kev-ju/PC-Retro-MTM/64_256KB_SYSTEM_BOARD.kicad_sch

## KiCad design 64_256KB_SYSTEM_BOARD.kicad_sch (2026-03-31)

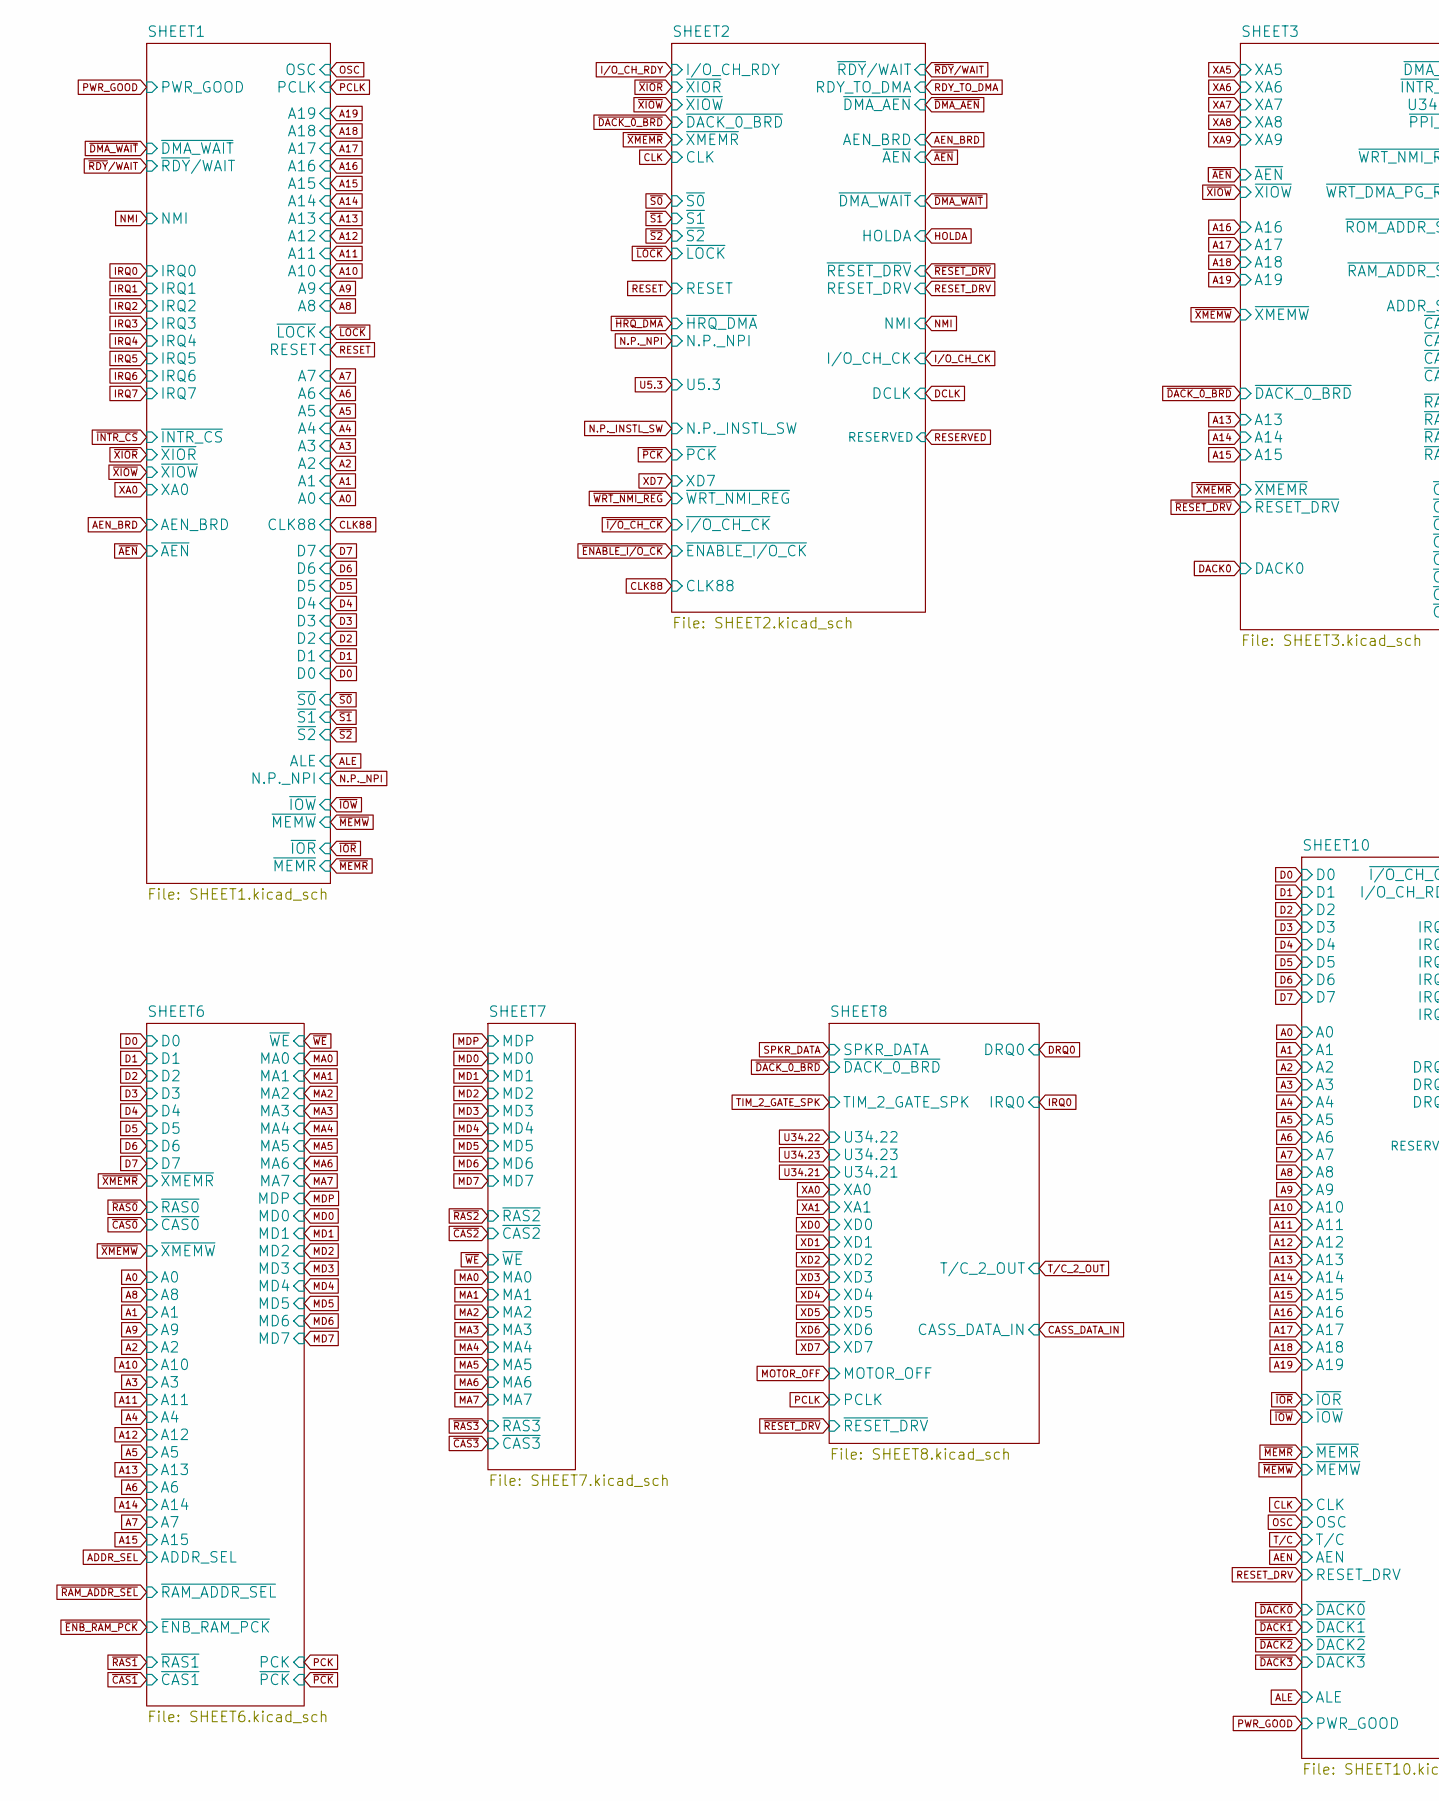
[picture p4: schematic 64_256KB_SYSTEM_BOARD.kicad_sch, part in row 1, column 1]

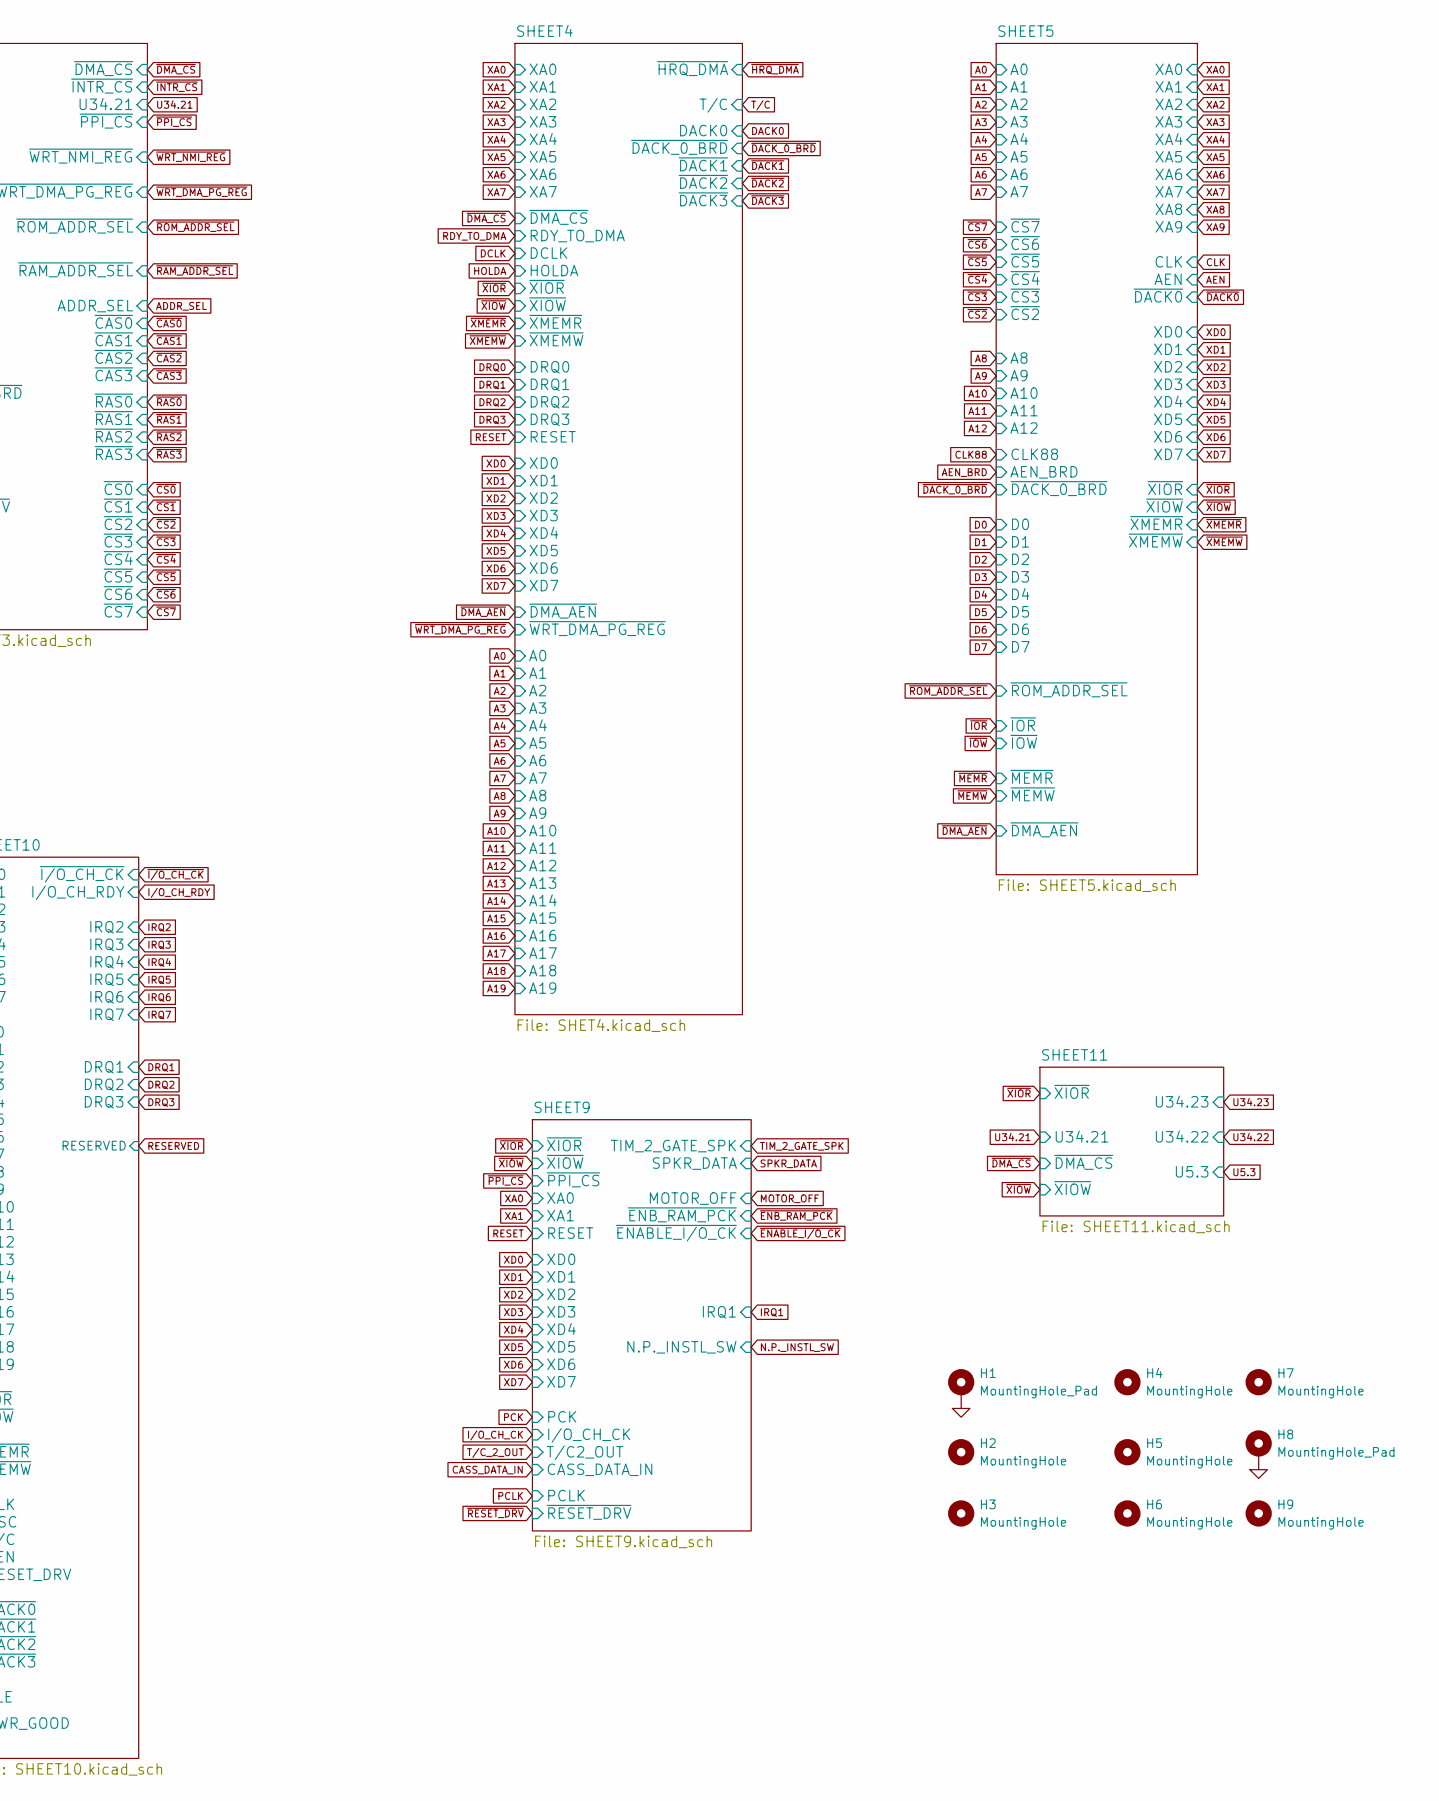
[picture p5: schematic 64_256KB_SYSTEM_BOARD.kicad_sch, part in row 1, column 2]

Parts:
H1, H8: MountingHole_Pad; PLATED_HOLE
H2, H3, H4, H5, H6, H7, H9: MountingHole; HOLE

Connections:
GND: H1.1, H8.1
