kev-ju/PC-Retro-MTM/SHEET1.kicad_sch

## KiCad design SHEET1.kicad_sch (2026-03-31)

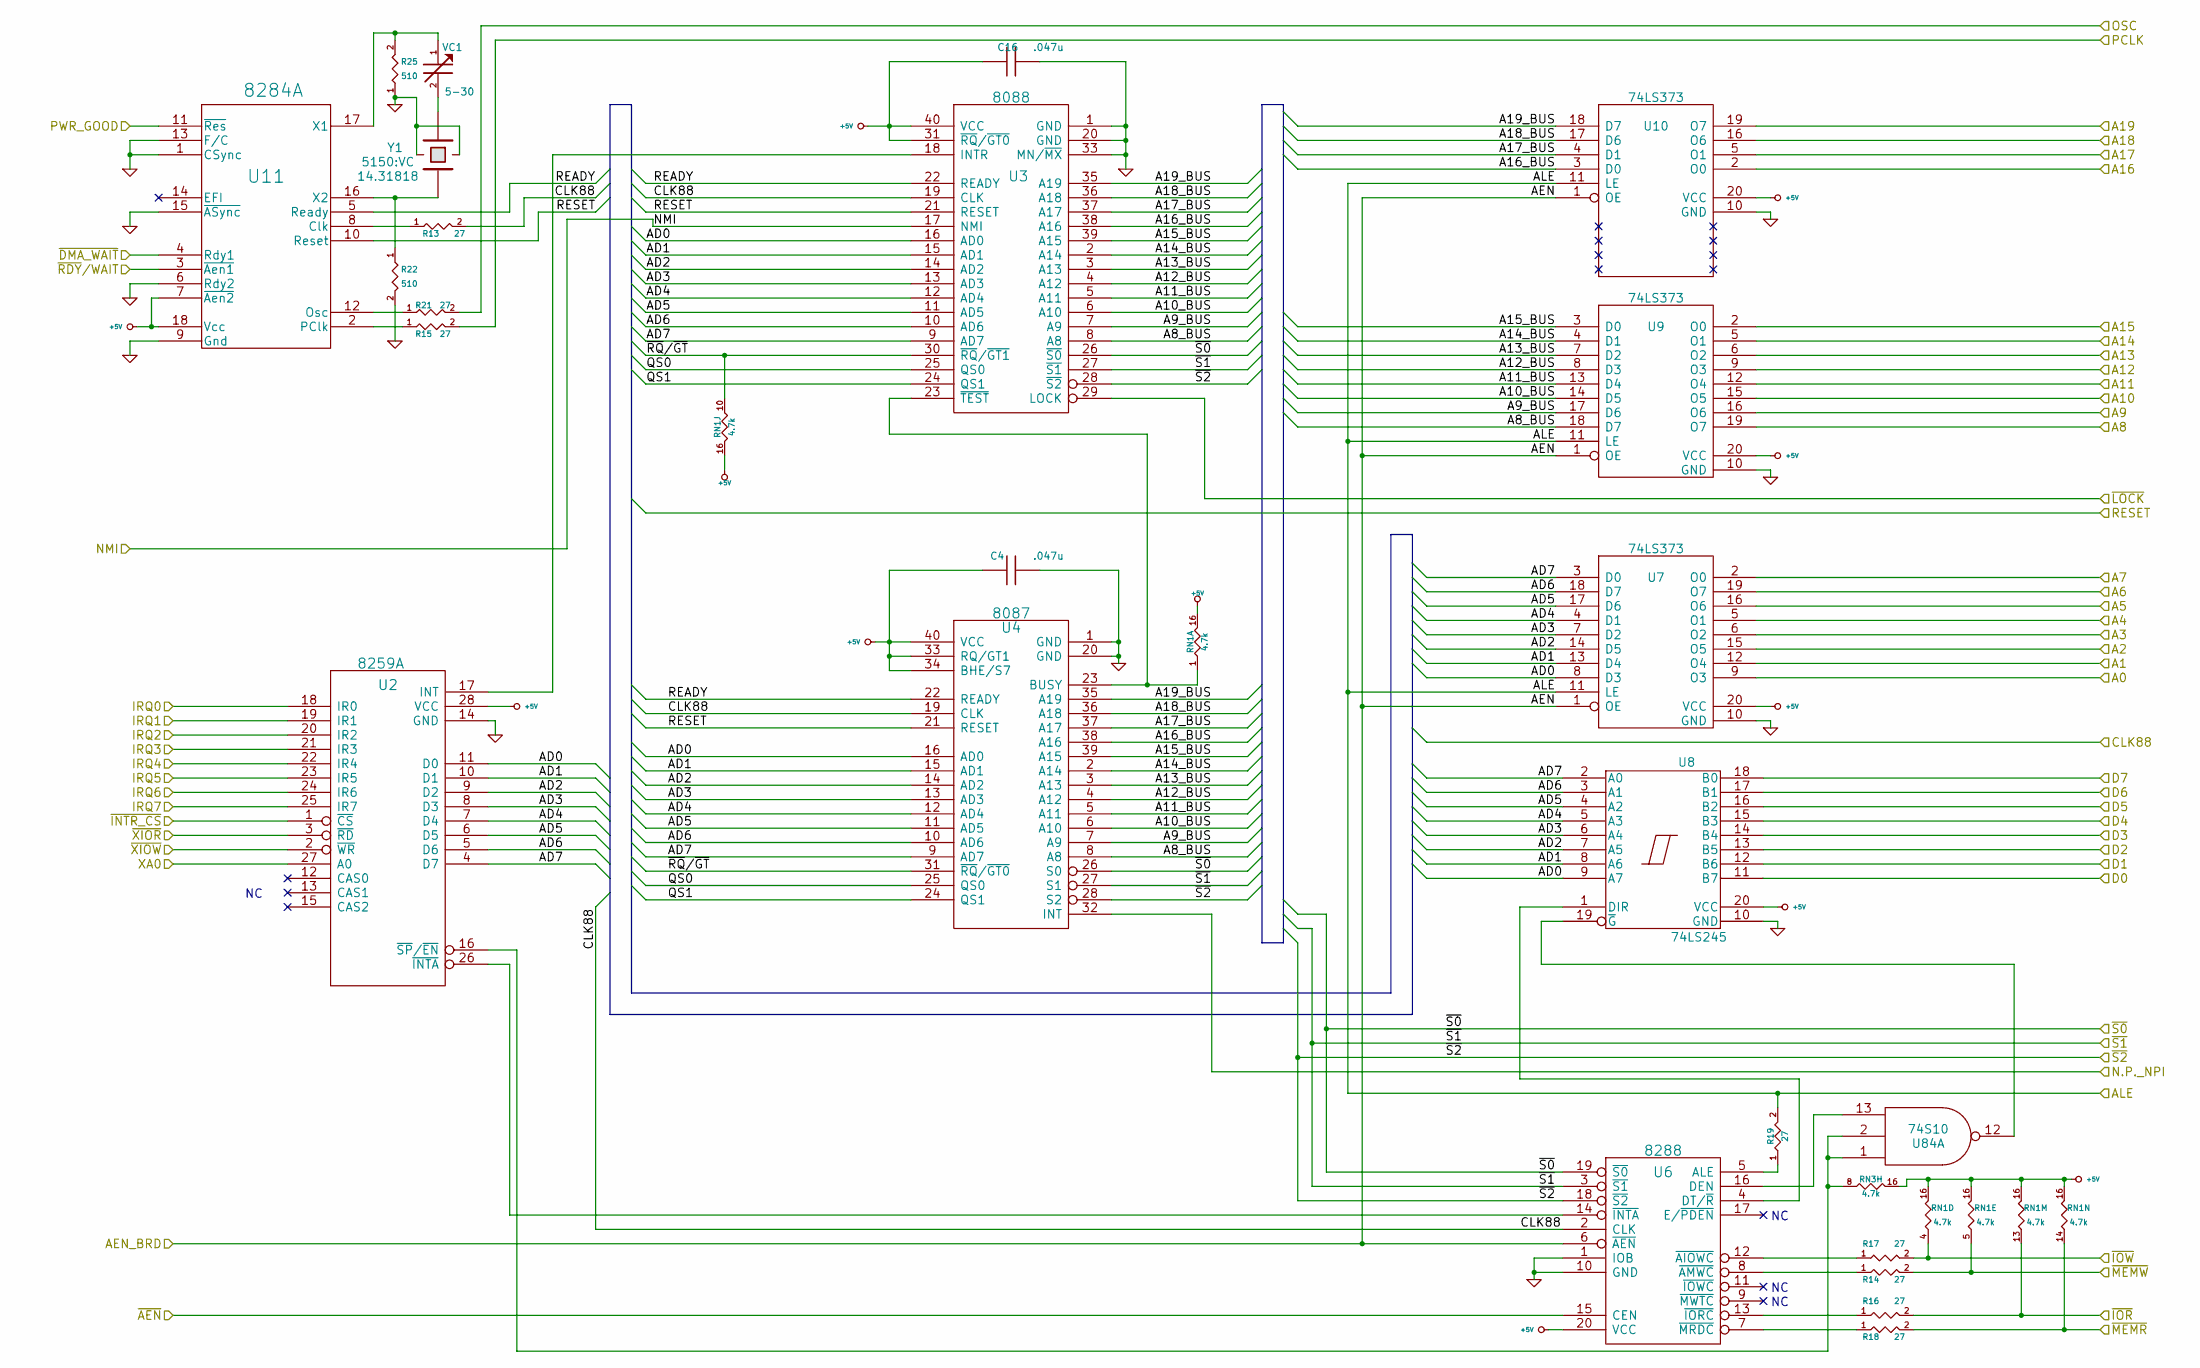
[picture p6: schematic SHEET1.kicad_sch]

Parts:
C4, C16: .047u; C_254_508_2PIN
R13, R14, R15, R16, R17, R18, R19, R21: 27; R5
R22, R25: 510; R5
RN1, RN3: 4.7k; DIP-16__300
U2: 8259A; DIP-28__600
U3: 8088; DIP-40__600
U4: 8087; DIP-40__600
U6: 8288; DIP-20__300
U7, U9, U10: 74LS373; DIP-20__300
U8: 74LS245; DIP-20__300
U11: 8284A; DIP-18__300
U84: 74S10; DIP-14__300
VC1: 5-30; VR
Y1: 14.31818; VC

Connections:
+5V: C4.2, C16.2, RN1.16, RN3.16, U2.28 (VCC), U3.31 (~RQ/~GT0), U3.40 (VCC), U4.33 (RQ/GT1), U4.34 (BHE/S7), U4.40 (VCC), U6.20 (VCC), U7.20 (VCC), U8.20 (VCC), U9.20 (VCC), U10.20 (VCC), U11.7 (~Aen2), U11.18 (Vcc)
A0: U7.9 (O3)
A1: U7.12 (O4)
A2: U7.15 (O5)
A3: U7.6 (O2)
A4: U7.5 (O1)
A5: U7.16 (O6)
A6: U7.19 (O7)
A7: U7.2 (O0)
A8: U9.19 (O7)
A8_BUS: U3.8 (A8), U4.8 (A8), U9.18 (D7)
A9: U9.16 (O6)
A9_BUS: U3.7 (A9), U4.7 (A9), U9.17 (D6)
A10: U9.15 (O5)
A10_BUS: U3.6 (A10), U4.6 (A10), U9.14 (D5)
A11: U9.12 (O4)
A11_BUS: U3.5 (A11), U4.5 (A11), U9.13 (D4)
A12: U9.9 (O3)
A12_BUS: U3.4 (A12), U4.4 (A12), U9.8 (D3)
A13: U9.6 (O2)
A13_BUS: U3.3 (A13), U4.3 (A13), U9.7 (D2)
A14: U9.5 (O1)
A14_BUS: U3.2 (A14), U4.2 (A14), U9.4 (D1)
A15: U9.2 (O0)
A15_BUS: U3.39 (A15), U4.39 (A15), U9.3 (D0)
A16: U10.2 (O0)
A16_BUS: U3.38 (A16), U4.38 (A16), U10.3 (D0)
A17: U10.5 (O1)
A17_BUS: U3.37 (A17), U4.37 (A17), U10.4 (D1)
A18: U10.16 (O6)
A18_BUS: U3.36 (A18), U4.36 (A18), U10.17 (D6)
A19: U10.19 (O7)
A19_BUS: U3.35 (A19), U4.35 (A19), U10.18 (D7)
AD0: U2.11 (D0), U3.16 (AD0), U4.16 (AD0), U7.8 (D3), U8.9 (A7)
AD1: U2.10 (D1), U3.15 (AD1), U4.15 (AD1), U7.13 (D4), U8.8 (A6)
AD2: U2.9 (D2), U3.14 (AD2), U4.14 (AD2), U7.14 (D5), U8.7 (A5)
AD3: U2.8 (D3), U3.13 (AD3), U4.13 (AD3), U7.7 (D2), U8.6 (A4)
AD4: U2.7 (D4), U3.12 (AD4), U4.12 (AD4), U7.4 (D1), U8.5 (A3)
AD5: U2.6 (D5), U3.11 (AD5), U4.11 (AD5), U7.17 (D6), U8.4 (A2)
AD6: U2.5 (D6), U3.10 (AD6), U4.10 (AD6), U7.18 (D7), U8.3 (A1)
AD7: U2.4 (D7), U3.9 (AD7), U4.9 (AD7), U7.3 (D0), U8.2 (A0)
AEN: U6.6 (~AEN), U7.1 (OE), U9.1 (OE), U10.1 (OE)
ALE: R19.2, U7.11 (LE), U9.11 (LE), U10.11 (LE)
CLK88: R13.2, U3.19 (CLK), U4.19 (CLK), U6.2 (CLK)
D0: U8.11 (B7)
D1: U8.12 (B6)
D2: U8.13 (B5)
D3: U8.14 (B4)
D4: U8.15 (B3)
D5: U8.16 (B2)
D6: U8.17 (B1)
D7: U8.18 (B0)
GND: C4.1, C16.1, R22.2, R25.1, U2.14 (GND), U3.1 (GND), U3.20 (GND), U3.33 (MN/~MX), U4.1 (GND), U4.20 (GND), U6.1 (IOB), U6.10 (GND), U7.10 (GND), U8.10 (GND), U9.10 (GND), U10.10 (GND), U11.1 (CSync), U11.6 (Rdy2), U11.9 (Gnd), U11.13 (F/C), U11.15 (~ASync), Y1.3 (GND), Y1.4 (GND)
IRQ0: U2.18 (IR0)
IRQ1: U2.19 (IR1)
IRQ2: U2.20 (IR2)
IRQ3: U2.21 (IR3)
IRQ4: U2.22 (IR4)
IRQ5: U2.23 (IR5)
IRQ6: U2.24 (IR6)
IRQ7: U2.25 (IR7)
N.P._NPI: U4.32 (INT)
NMI: U3.17 (NMI)
unnamed: R13.1, U11.8 (Clk)
unnamed: R14.1, U6.8 (~AMWC)
unnamed: R15.1, U11.2 (PClk)
unnamed: R16.1, U6.13 (~IORC)
unnamed: R17.1, U6.12 (~AIOWC)
unnamed: R18.1, U6.7 (~MRDC)
unnamed: R19.1, U6.5 (ALE)
unnamed: R21.1, U11.12 (Osc)
unnamed: R22.1, U11.16 (X2), Y1.2
unnamed: R25.2, U11.17 (X1), VC1.1
unnamed: RN1.1 (P15), U3.23 (~TEST), U4.23 (BUSY)
unnamed: RN3.8 (P15), U2.16 (~SP/~EN), U84.1, U84.2
unnamed: U2.17 (INT), U3.18 (INTR)
unnamed: U2.26 (~INTA), U6.14 (~INTA)
unnamed: U6.4 (DT/~R), U8.1 (DIR)
unnamed: U6.16 (DEN), U84.13
unnamed: U8.19 (~G), U84.12
unnamed: VC1.2, Y1.1
OSC: R21.2
PCLK: R15.2
PWR_GOOD: U11.11 (~Res)
QS0: U3.25 (QS0), U4.25 (QS0)
QS1: U3.24 (QS1), U4.24 (QS1)
READY: U3.22 (READY), U4.22 (READY), U11.5 (Ready)
RESET: U3.21 (RESET), U4.21 (RESET), U11.10 (Reset)
XA0: U2.27 (A0)
~AEN: U6.15 (CEN)
~DMA_WAIT: U11.4 (Rdy1)
~INTR_CS: U2.1 (~CS)
~IOR: R16.2, RN1.13 (P15)
~IOW: R17.2, RN1.4 (P15)
~LOCK: U3.29 (LOCK)
~MEMR: R18.2, RN1.14 (P15)
~MEMW: R14.2, RN1.5 (P15)
~RDY/WAIT: U11.3 (~Aen1)
~RQ/~GT: RN1.10 (P15), U3.30 (~RQ/~GT1), U4.31 (~RQ/~GT0)
~S0: U3.26 (~S0), U4.26 (S0), U6.19 (~S0)
~S1: U3.27 (~S1), U4.27 (S1), U6.3 (~S1)
~S2: U3.28 (~S2), U4.28 (S2), U6.18 (~S2)
~XIOR: U2.3 (~RD)
~XIOW: U2.2 (~WR)
