kev-ju/PC-Retro-MTM/SHEET2.kicad_sch

## KiCad design SHEET2.kicad_sch (2026-03-31)

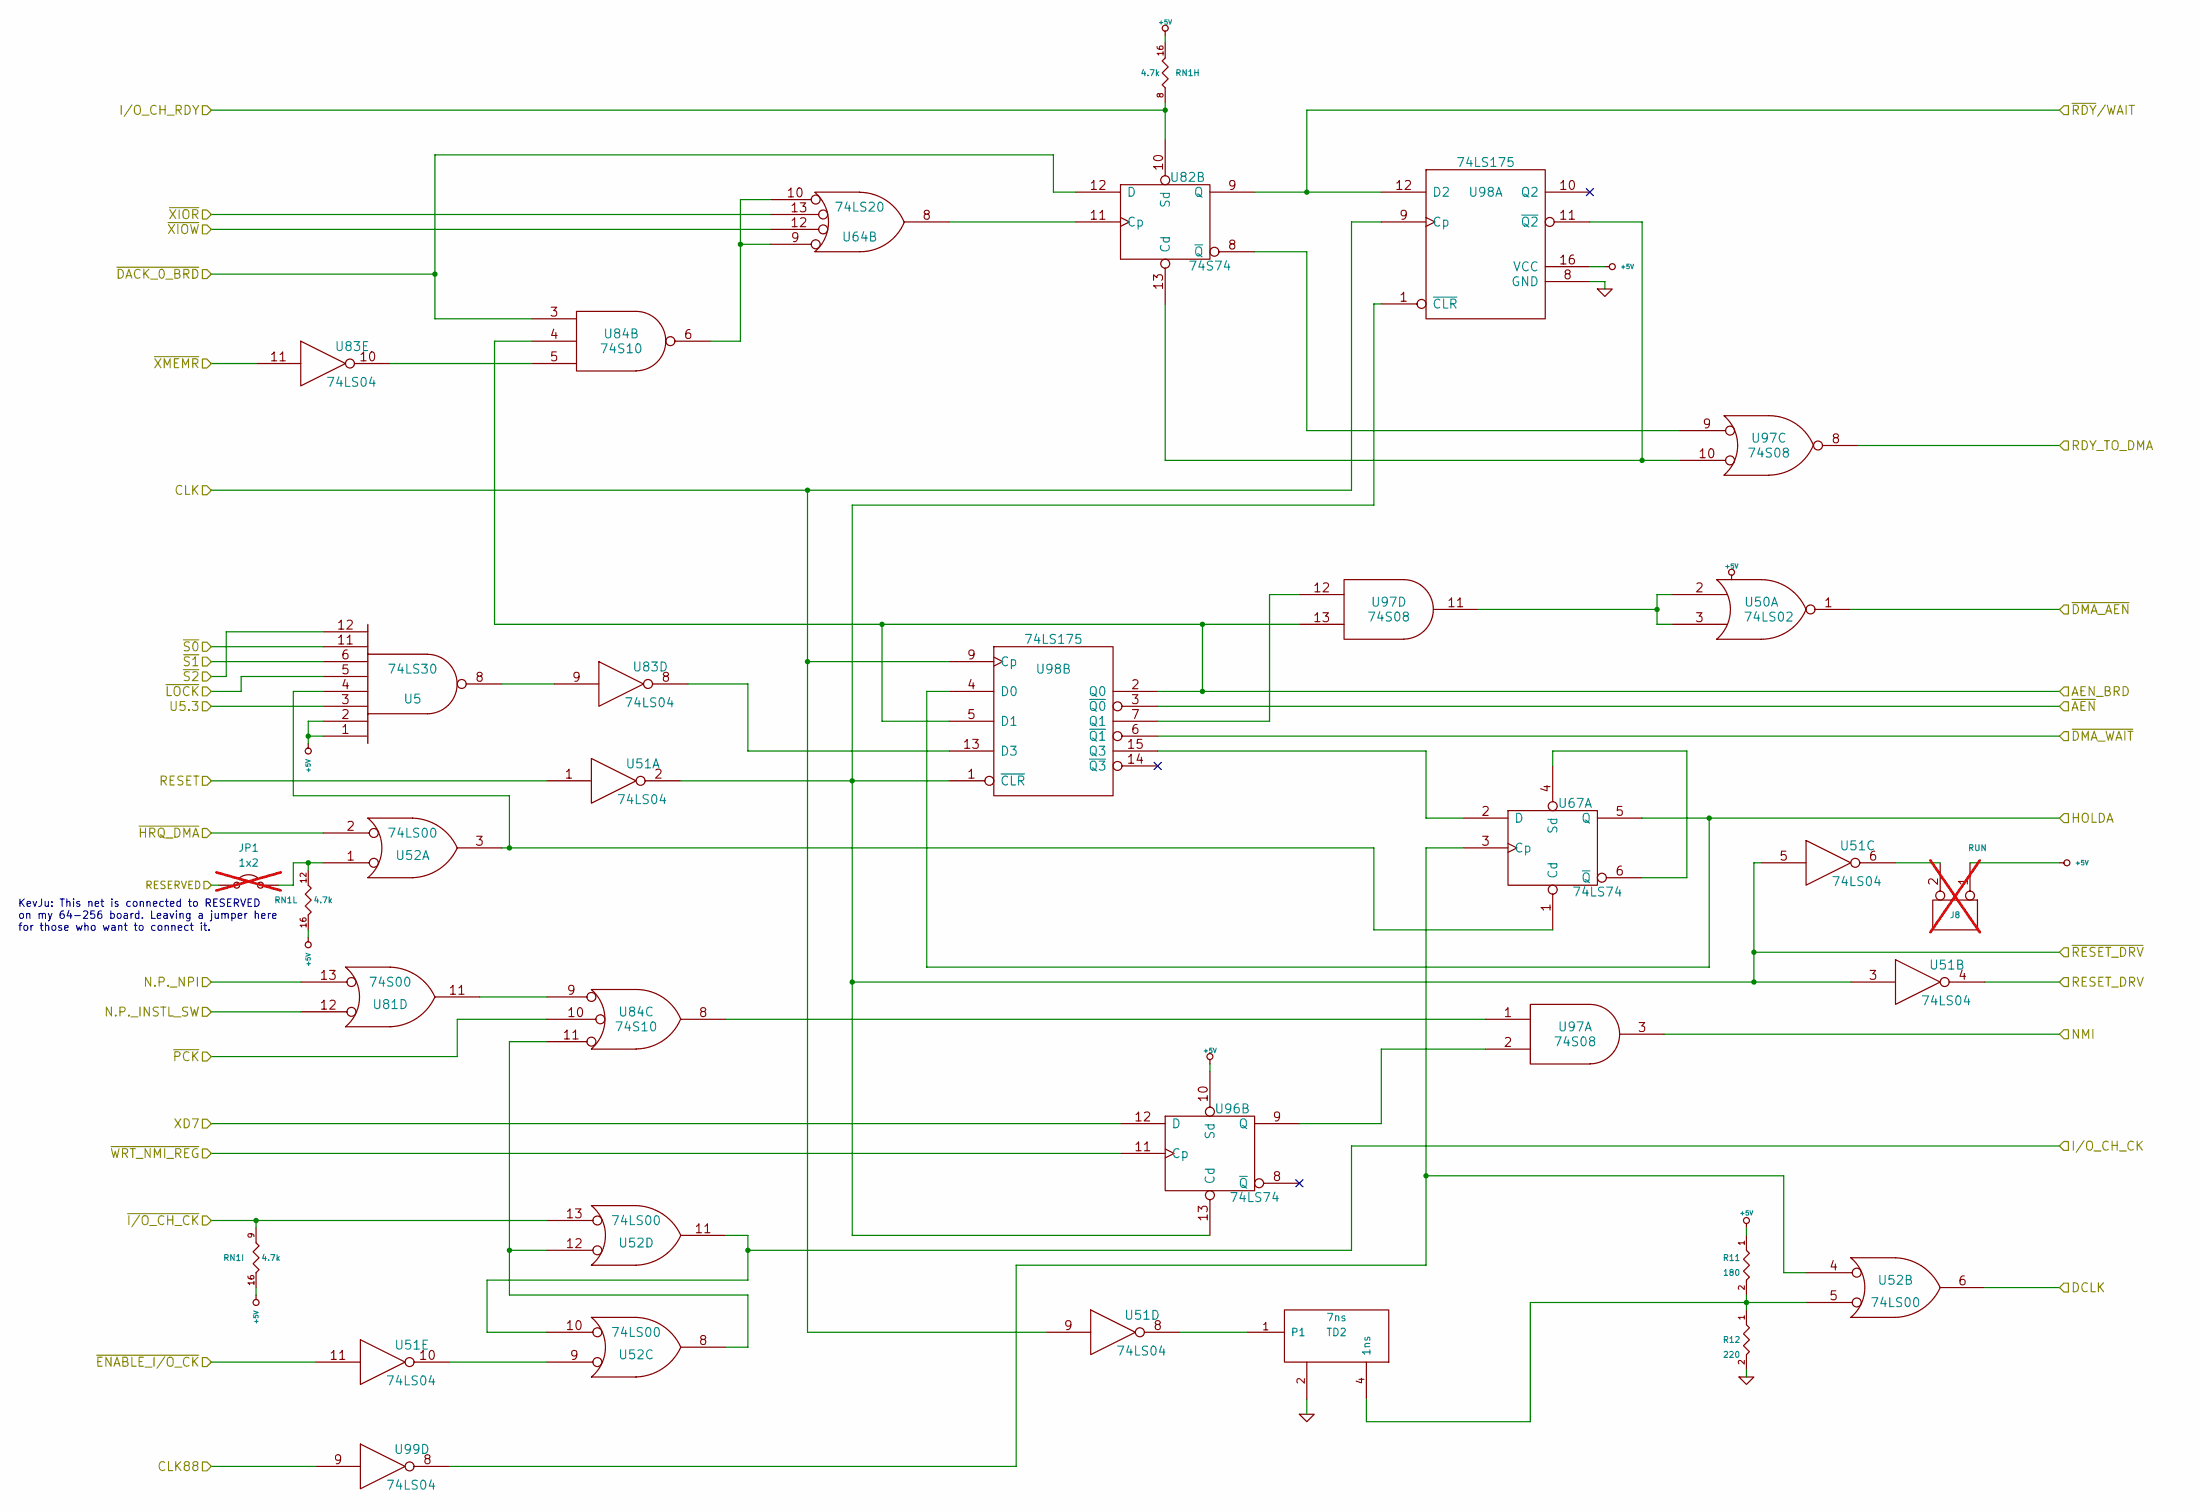
[picture p7: schematic SHEET2.kicad_sch]

Parts:
J8: RUN; PIN_ARRAY_2X1; not fitted
JP1: 1x2; PinHeader_1x02_P2.54mm_Vertical; not fitted
R11: 180; R5
R12: 220; R5
RN1: 4.7k; DIP-16__300
TD2: 7ns; TD2
U5: 74LS30; DIP-14__300
U50: 74LS02; DIP-14__300
U51, U83, U99: 74LS04; DIP-14__300
U52: 74LS00; DIP-14__300
U64: 74LS20; DIP-14__300
U67, U96: 74LS74; DIP-14__300
U81: 74S00; DIP-14__300
U82: 74S74; DIP-14__300
U84: 74S10; DIP-14__300
U97: 74S08; DIP-14__300
U98: 74LS175; DIP-16__300

Connections:
+5V: J8.1, R11.1, RN1.16, U5.1, U5.2, U50.14 (VCC), U96.10 (Sd), U98.16 (VCC)
AEN_BRD: U84.4, U97.13, U98.2 (Q0), U98.5 (D1)
CLK: U51.9, U98.9 (Cp)
CLK88: U99.9
DCLK: U52.6
GND: R12.2, TD2.2, U98.8 (GND)
HOLDA: U67.5 (Q), U98.4 (D0)
I/O_CH_CK: U52.10, U52.11
I/O_CH_RDY: RN1.8 (P15), U82.10 (Sd)
N.P._INSTL_SW: U81.12
N.P._NPI: U81.13
NMI: U97.3
unnamed: J8.2 (PM), U51.6
unnamed: JP1.2 (B), RN1.12 (P15), U52.1
unnamed: R11.2, R12.1, TD2.4 (1ns), U52.5
unnamed: TD2.1, U51.8
unnamed: U5.4, U52.3, U67.1 (Cd)
unnamed: U5.8, U83.9
unnamed: U50.2, U50.3, U97.11
unnamed: U51.10, U52.9
unnamed: U52.4, U67.3 (Cp), U99.8
unnamed: U52.8, U52.12, U84.11
unnamed: U64.8, U82.11 (Cp)
unnamed: U64.9, U64.13, U84.6
unnamed: U67.2 (D), U98.15 (Q3)
unnamed: U67.4 (Sd), U67.6 (~Q)
unnamed: U81.11, U84.9
unnamed: U82.8 (~Q), U97.9
unnamed: U82.13 (Cd), U97.10, U98.11 (~Q2)
unnamed: U83.8, U98.13 (D3)
unnamed: U83.10, U84.5
unnamed: U84.8, U97.1
unnamed: U96.9 (Q), U97.2
unnamed: U97.12, U98.7 (Q1)
RDY_TO_DMA: U97.8
RESERVED: JP1.1 (A)
RESET: U51.1
RESET_DRV: U51.4
U5.3: U5.3
XD7: U96.12 (D)
~AEN: U98.3 (~Q0)
~DACK_0_BRD: U82.12 (D), U84.3
~DMA_AEN: U50.1
~DMA_WAIT: U98.6 (~Q1)
~ENABLE_I/O_CK: U51.11
~HRQ_DMA: U52.2
~I/O_CH_CK: RN1.9 (P15), U52.13
~LOCK: U5.5
~PCK: U84.10
~RDY/WAIT: U82.9 (Q), U98.12 (D2)
~RESET_DRV: U51.2, U51.3, U51.5, U96.13 (Cd), U98.1 (~CLR)
~S0: U5.11
~S1: U5.6
~S2: U5.12
~WRT_NMI_REG: U96.11 (Cp)
~XIOR: U64.12
~XIOW: U64.10
~XMEMR: U83.11

Notes on the sheet:
KevJu: This net is connected to RESERVED on my 64-256 board. Leaving a jumper here for those who want to connect it.
