kev-ju/PC-Retro-MTM/SHEET3.kicad_sch

## KiCad design SHEET3.kicad_sch (2026-03-31)

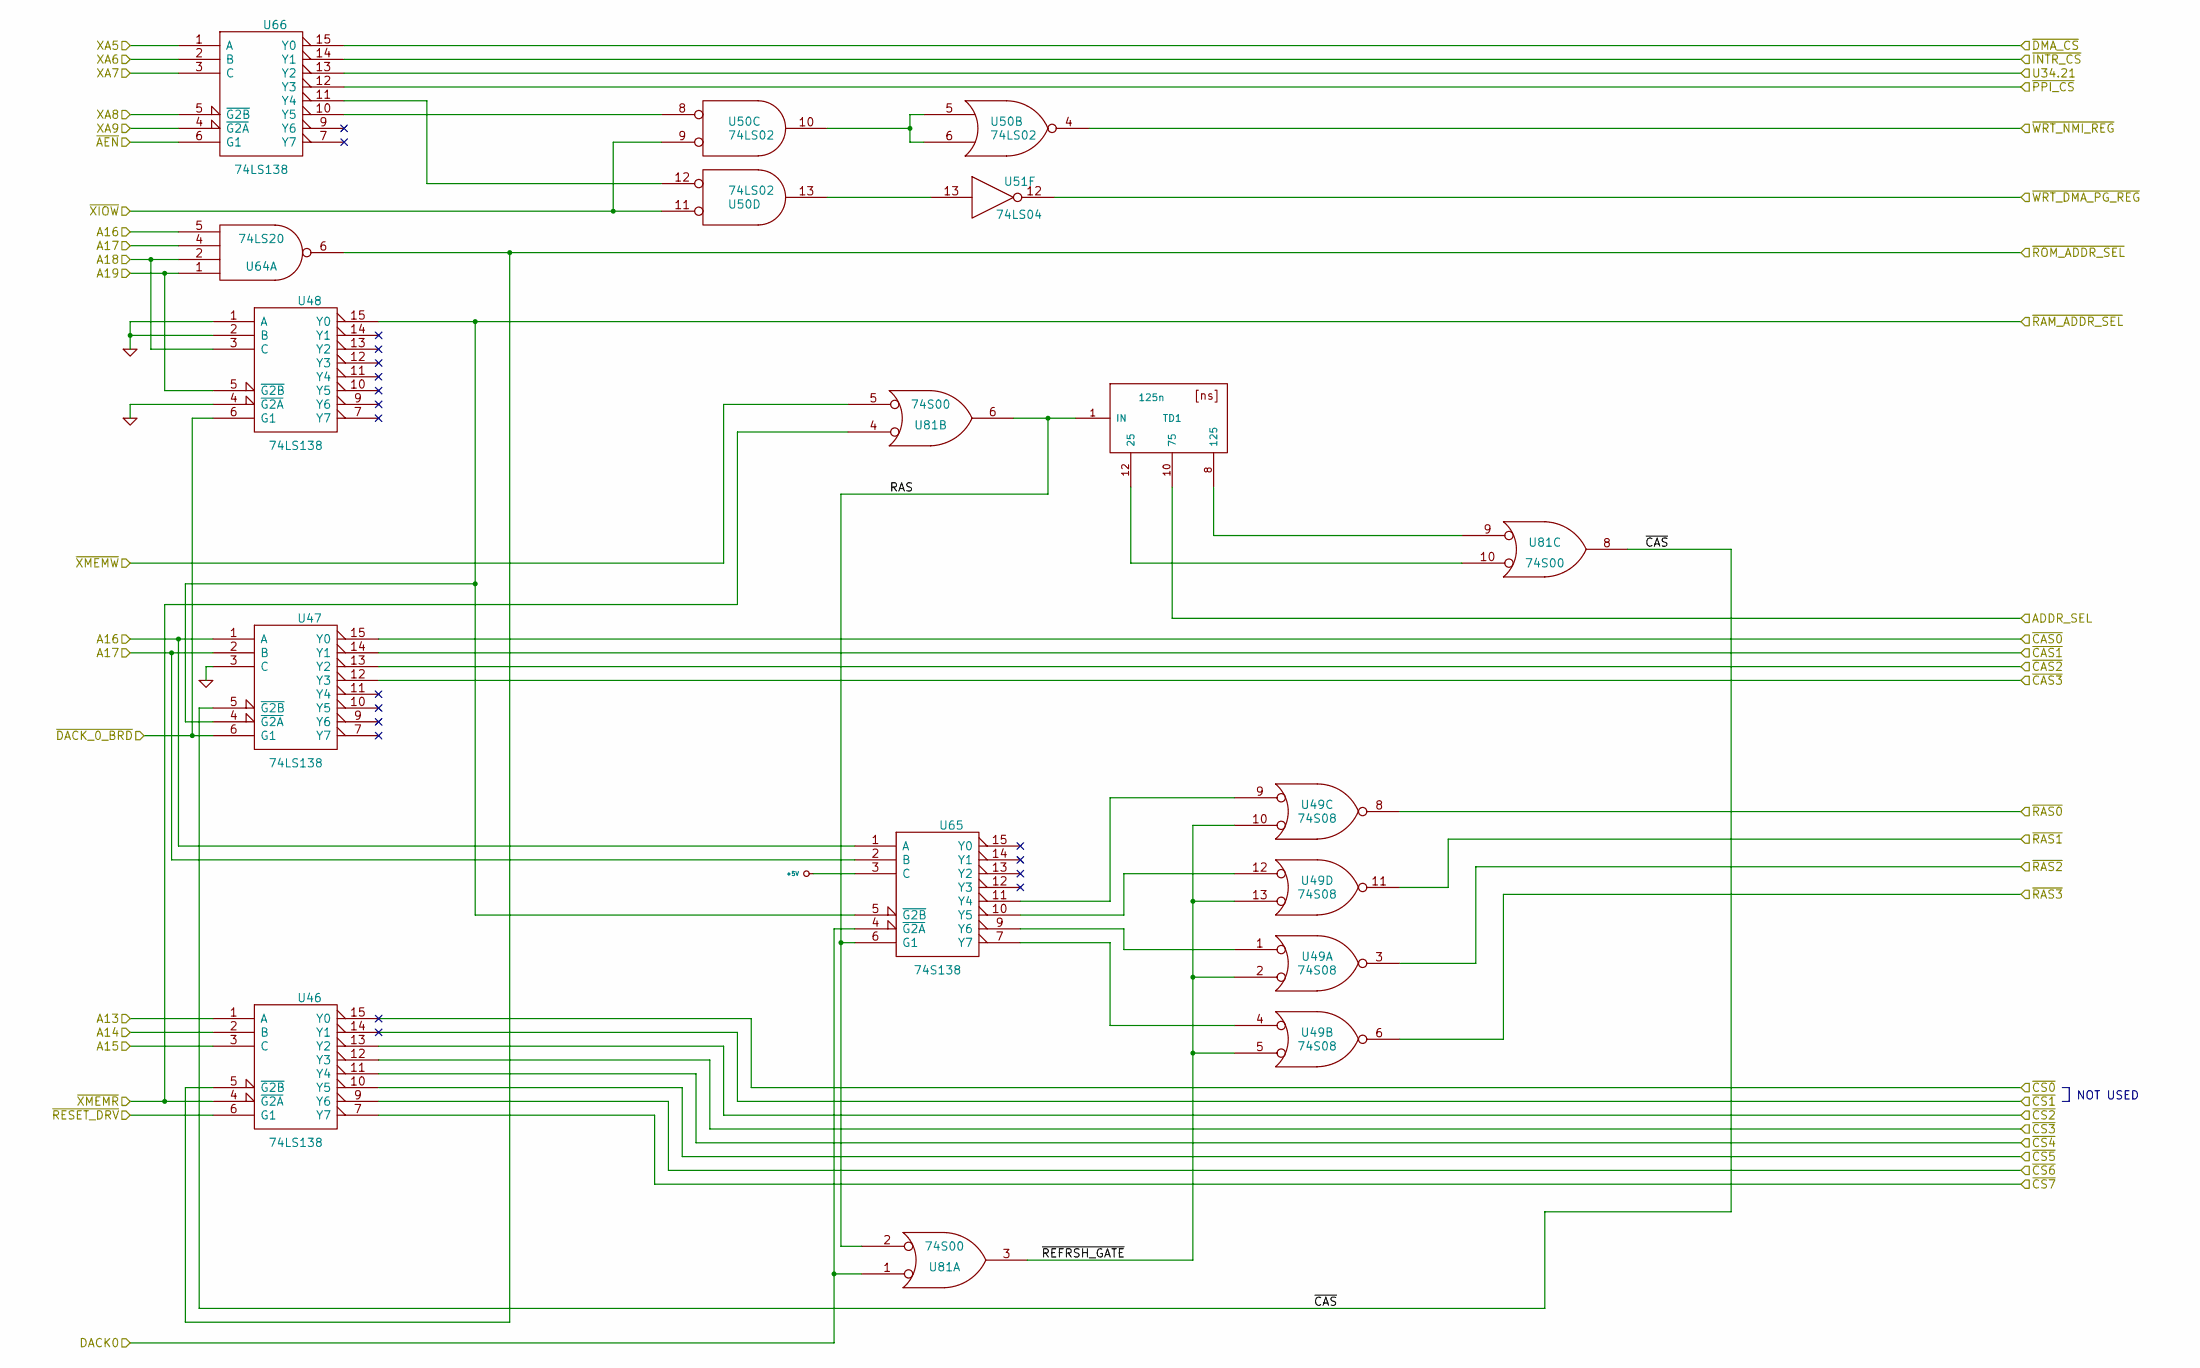
[picture p8: schematic SHEET3.kicad_sch]

Parts:
TD1: 125n; TD1
U46, U47, U48, U66: 74LS138; DIP-16__300
U49: 74S08; DIP-14__300
U50: 74LS02; DIP-14__300
U51: 74LS04; DIP-14__300
U64: 74LS20; DIP-14__300
U65: 74S138; DIP-16__300
U81: 74S00; DIP-14__300

Connections:
+5V: U65.3 (C)
A13: U46.1 (A)
A14: U46.2 (B)
A15: U46.3 (C)
A16: U47.1 (A), U64.5, U65.1 (A)
A17: U47.2 (B), U64.4, U65.2 (B)
A18: U48.3 (C), U64.2
A19: U48.5 (~G2B), U64.1
ADDR_SEL: TD1.10 (75)
DACK0: U65.4 (~G2A), U81.1
GND: U47.3 (C), U48.1 (A), U48.2 (B), U48.4 (~G2A)
unnamed: TD1.8 (125), U81.9
unnamed: TD1.12 (25), U81.10
unnamed: U49.1, U65.9 (Y6)
unnamed: U49.4, U65.7 (Y7)
unnamed: U49.9, U65.11 (Y4)
unnamed: U49.12, U65.10 (Y5)
unnamed: U50.8, U66.10 (Y5)
unnamed: U50.5, U50.6, U50.10
unnamed: U50.12, U66.11 (Y4)
unnamed: U50.13, U51.13
RAS: TD1.1 (IN), U65.6 (G1), U81.2, U81.6
U34.21: U66.13 (Y2)
XA5: U66.1 (A)
XA6: U66.2 (B)
XA7: U66.3 (C)
XA8: U66.5 (~G2B)
XA9: U66.4 (~G2A)
~AEN: U66.6 (G1)
~CAS0: U47.15 (Y0)
~CAS1: U47.14 (Y1)
~CAS2: U47.13 (Y2)
~CAS3: U47.12 (Y3)
~CAS: U47.5 (~G2B), U81.8
~CS0: U46.15 (Y0)
~CS1: U46.14 (Y1)
~CS2: U46.13 (Y2)
~CS3: U46.12 (Y3)
~CS4: U46.11 (Y4)
~CS5: U46.10 (Y5)
~CS6: U46.9 (Y6)
~CS7: U46.7 (Y7)
~DACK_0_BRD: U47.6 (G1), U48.6 (G1)
~DMA_CS: U66.15 (Y0)
~INTR_CS: U66.14 (Y1)
~PPI_CS: U66.12 (Y3)
~RAM_ADDR_SEL: U47.4 (~G2A), U48.15 (Y0), U65.5 (~G2B)
~RAS0: U49.8
~RAS1: U49.11
~RAS2: U49.3
~RAS3: U49.6
~REFRSH_GATE: U49.2, U49.5, U49.10, U49.13, U81.3
~RESET_DRV: U46.6 (G1)
~ROM_ADDR_SEL: U46.5 (~G2B), U64.6
~WRT_DMA_PG_REG: U51.12
~WRT_NMI_REG: U50.4
~XIOW: U50.9, U50.11
~XMEMR: U46.4 (~G2A), U81.4
~XMEMW: U81.5

Notes on the sheet:
NOT USED
