kev-ju/PC-Retro-MTM/SHEET5.kicad_sch

## KiCad design SHEET5.kicad_sch (2026-03-31)

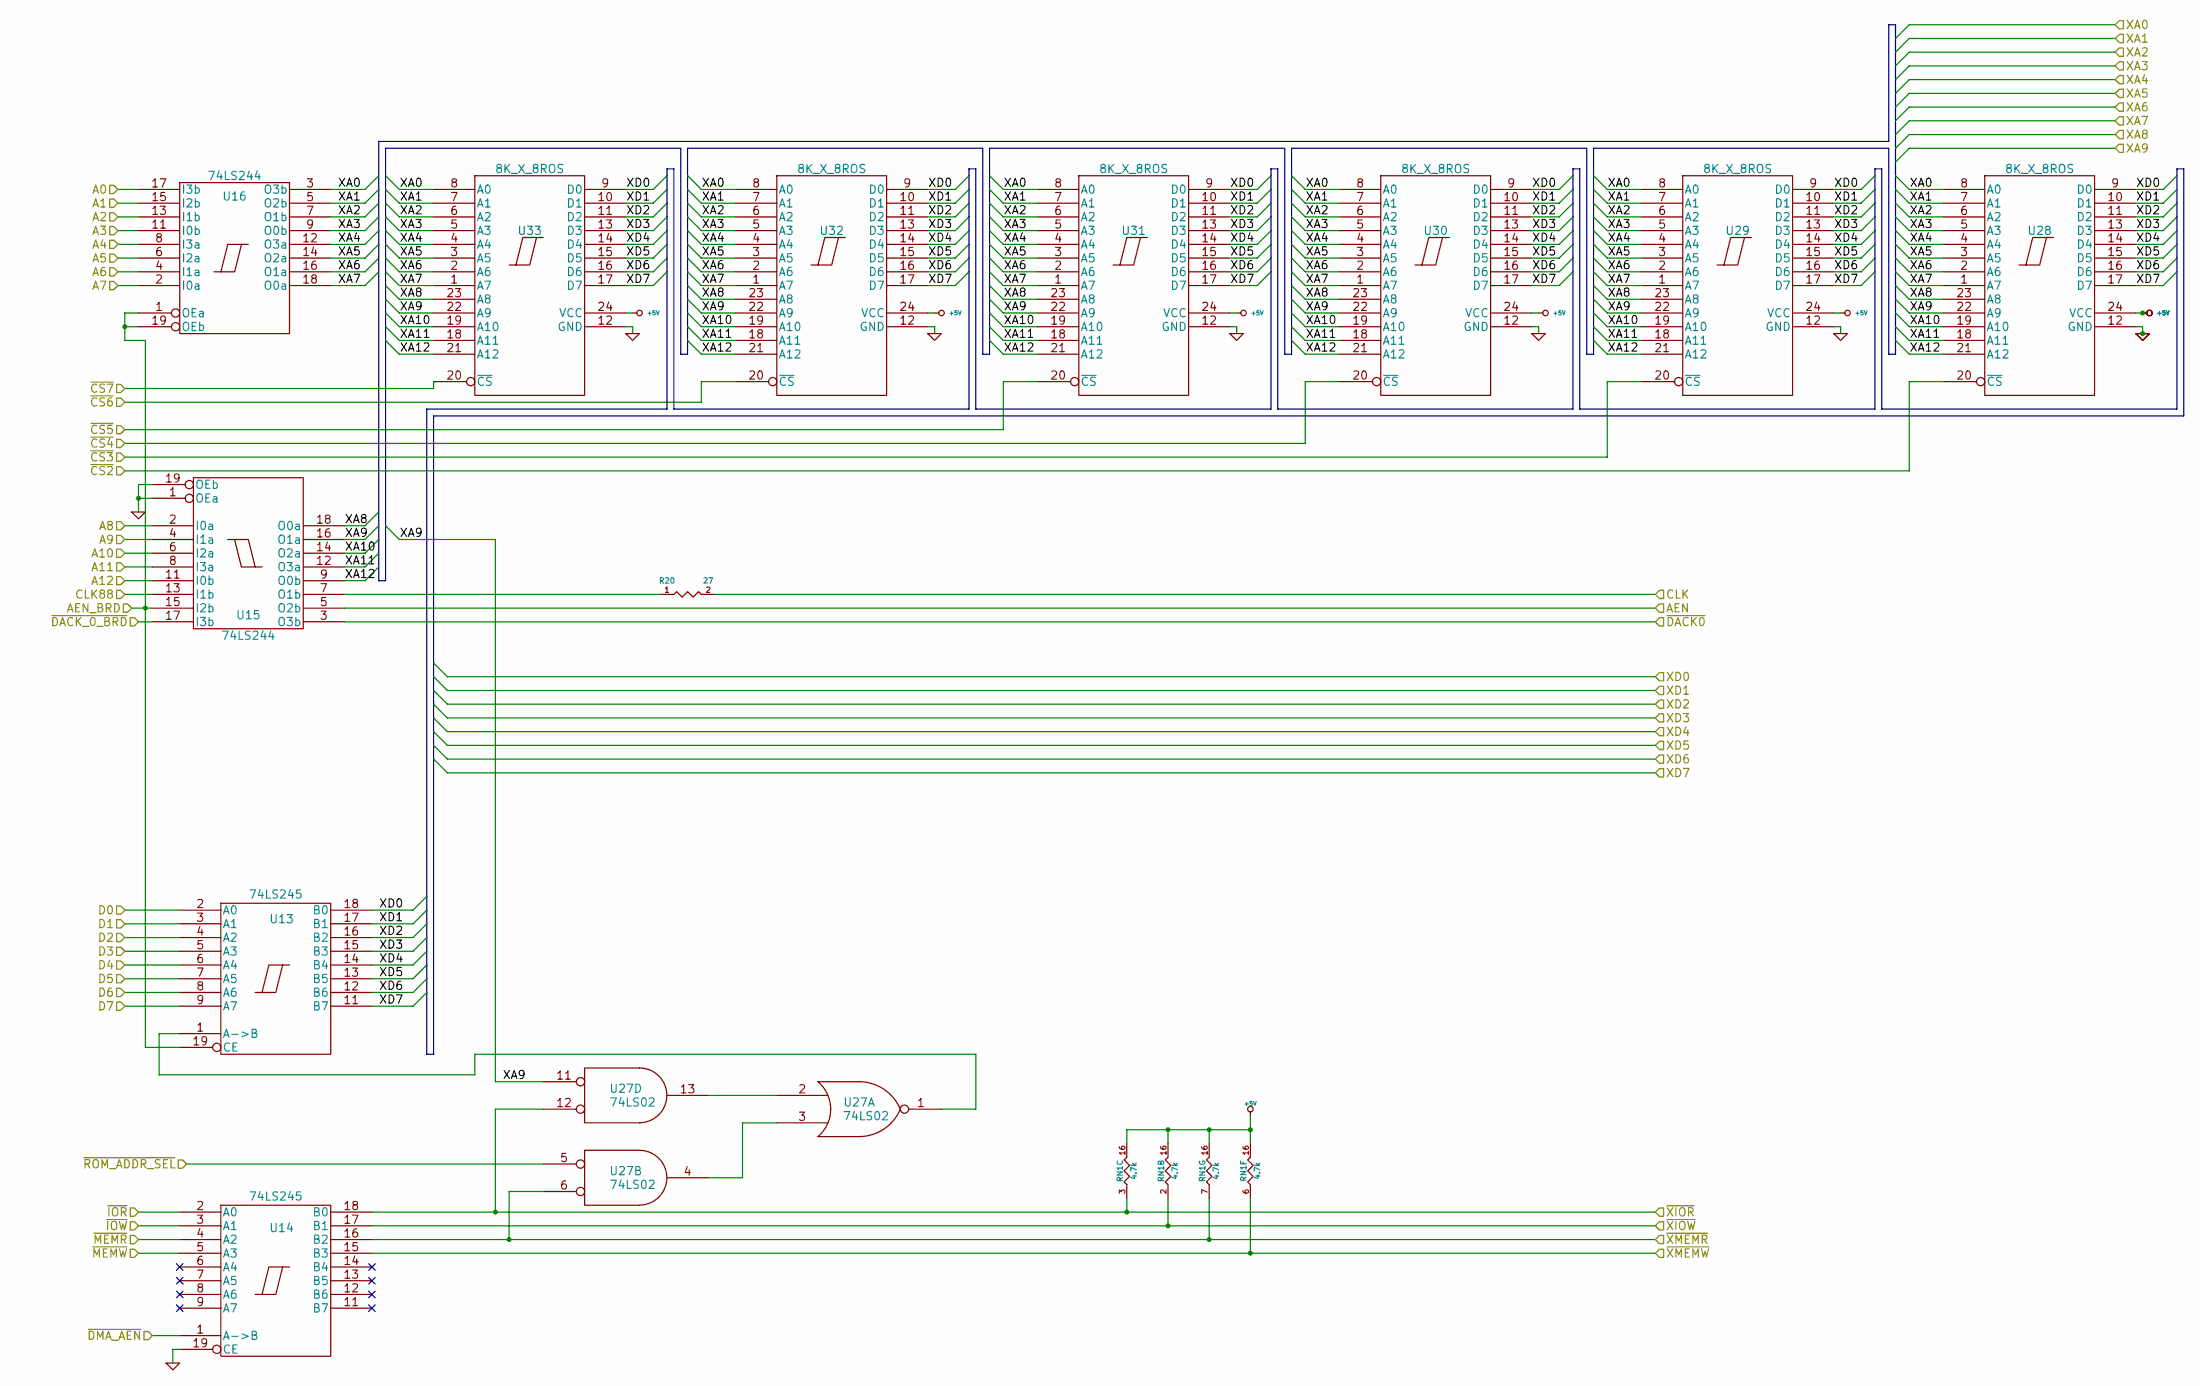
[picture p9: schematic SHEET5.kicad_sch]

Parts:
R20: 27; R5
RN1: 4.7k; DIP-16__300
U13, U14: 74LS245; DIP-20__300
U15, U16: 74LS244; DIP-20__300
U27: 74LS02; DIP-14__300
U28, U29, U30, U31, U32, U33: 8K_X_8ROS; DIP-24__600

Connections:
+5V: RN1.16, U28.24 (VCC), U29.24 (VCC), U30.24 (VCC), U31.24 (VCC), U32.24 (VCC), U33.24 (VCC)
A0: U16.17 (I3b)
A1: U16.15 (I2b)
A2: U16.13 (I1b)
A3: U16.11 (I0b)
A4: U16.8 (I3a)
A5: U16.6 (I2a)
A6: U16.4 (I1a)
A7: U16.2 (I0a)
A8: U15.2 (I0a)
A9: U15.4 (I1a)
A10: U15.6 (I2a)
A11: U15.8 (I3a)
A12: U15.11 (I0b)
AEN: U15.5 (O2b)
AEN_BRD: U13.19 (CE), U15.15 (I2b), U16.1 (OEa), U16.19 (OEb)
CLK: R20.2
CLK88: U15.13 (I1b)
D0: U13.2 (A0)
D1: U13.3 (A1)
D2: U13.4 (A2)
D3: U13.5 (A3)
D4: U13.6 (A4)
D5: U13.7 (A5)
D6: U13.8 (A6)
D7: U13.9 (A7)
GND: U14.19 (CE), U15.1 (OEa), U15.19 (OEb), U28.12 (GND), U29.12 (GND), U30.12 (GND), U31.12 (GND), U32.12 (GND), U33.12 (GND)
unnamed: R20.1, U15.7 (O1b)
unnamed: U13.1 (A->B), U27.1
unnamed: U27.3, U27.4
unnamed: U27.2, U27.13
XA0: U16.3 (O3b), U28.8 (A0), U29.8 (A0), U30.8 (A0), U31.8 (A0), U32.8 (A0), U33.8 (A0)
XA1: U16.5 (O2b), U28.7 (A1), U29.7 (A1), U30.7 (A1), U31.7 (A1), U32.7 (A1), U33.7 (A1)
XA2: U16.7 (O1b), U28.6 (A2), U29.6 (A2), U30.6 (A2), U31.6 (A2), U32.6 (A2), U33.6 (A2)
XA3: U16.9 (O0b), U28.5 (A3), U29.5 (A3), U30.5 (A3), U31.5 (A3), U32.5 (A3), U33.5 (A3)
XA4: U16.12 (O3a), U28.4 (A4), U29.4 (A4), U30.4 (A4), U31.4 (A4), U32.4 (A4), U33.4 (A4)
XA5: U16.14 (O2a), U28.3 (A5), U29.3 (A5), U30.3 (A5), U31.3 (A5), U32.3 (A5), U33.3 (A5)
XA6: U16.16 (O1a), U28.2 (A6), U29.2 (A6), U30.2 (A6), U31.2 (A6), U32.2 (A6), U33.2 (A6)
XA7: U16.18 (O0a), U28.1 (A7), U29.1 (A7), U30.1 (A7), U31.1 (A7), U32.1 (A7), U33.1 (A7)
XA8: U15.18 (O0a), U28.23 (A8), U29.23 (A8), U30.23 (A8), U31.23 (A8), U32.23 (A8), U33.23 (A8)
XA9: U15.16 (O1a), U27.11, U28.22 (A9), U29.22 (A9), U30.22 (A9), U31.22 (A9), U32.22 (A9), U33.22 (A9)
XA10: U15.14 (O2a), U28.19 (A10), U29.19 (A10), U30.19 (A10), U31.19 (A10), U32.19 (A10), U33.19 (A10)
XA11: U15.12 (O3a), U28.18 (A11), U29.18 (A11), U30.18 (A11), U31.18 (A11), U32.18 (A11), U33.18 (A11)
XA12: U15.9 (O0b), U28.21 (A12), U29.21 (A12), U30.21 (A12), U31.21 (A12), U32.21 (A12), U33.21 (A12)
XD0: U13.18 (B0), U28.9 (D0), U29.9 (D0), U30.9 (D0), U31.9 (D0), U32.9 (D0), U33.9 (D0)
XD1: U13.17 (B1), U28.10 (D1), U29.10 (D1), U30.10 (D1), U31.10 (D1), U32.10 (D1), U33.10 (D1)
XD2: U13.16 (B2), U28.11 (D2), U29.11 (D2), U30.11 (D2), U31.11 (D2), U32.11 (D2), U33.11 (D2)
XD3: U13.15 (B3), U28.13 (D3), U29.13 (D3), U30.13 (D3), U31.13 (D3), U32.13 (D3), U33.13 (D3)
XD4: U13.14 (B4), U28.14 (D4), U29.14 (D4), U30.14 (D4), U31.14 (D4), U32.14 (D4), U33.14 (D4)
XD5: U13.13 (B5), U28.15 (D5), U29.15 (D5), U30.15 (D5), U31.15 (D5), U32.15 (D5), U33.15 (D5)
XD6: U13.12 (B6), U28.16 (D6), U29.16 (D6), U30.16 (D6), U31.16 (D6), U32.16 (D6), U33.16 (D6)
XD7: U13.11 (B7), U28.17 (D7), U29.17 (D7), U30.17 (D7), U31.17 (D7), U32.17 (D7), U33.17 (D7)
~CS2: U28.20 (~CS)
~CS3: U29.20 (~CS)
~CS4: U30.20 (~CS)
~CS5: U31.20 (~CS)
~CS6: U32.20 (~CS)
~CS7: U33.20 (~CS)
~DACK0: U15.3 (O3b)
~DACK_0_BRD: U15.17 (I3b)
~DMA_AEN: U14.1 (A->B)
~IOR: U14.2 (A0)
~IOW: U14.3 (A1)
~MEMR: U14.4 (A2)
~MEMW: U14.5 (A3)
~ROM_ADDR_SEL: U27.5
~XIOR: RN1.3 (P15), U14.18 (B0), U27.12
~XIOW: RN1.2 (P15), U14.17 (B1)
~XMEMR: RN1.7 (P15), U14.16 (B2), U27.6
~XMEMW: RN1.6 (P15), U14.15 (B3)
