kev-ju/PC-Retro-MTM/SHEET6.kicad_sch

## KiCad design SHEET6.kicad_sch (2026-03-31)

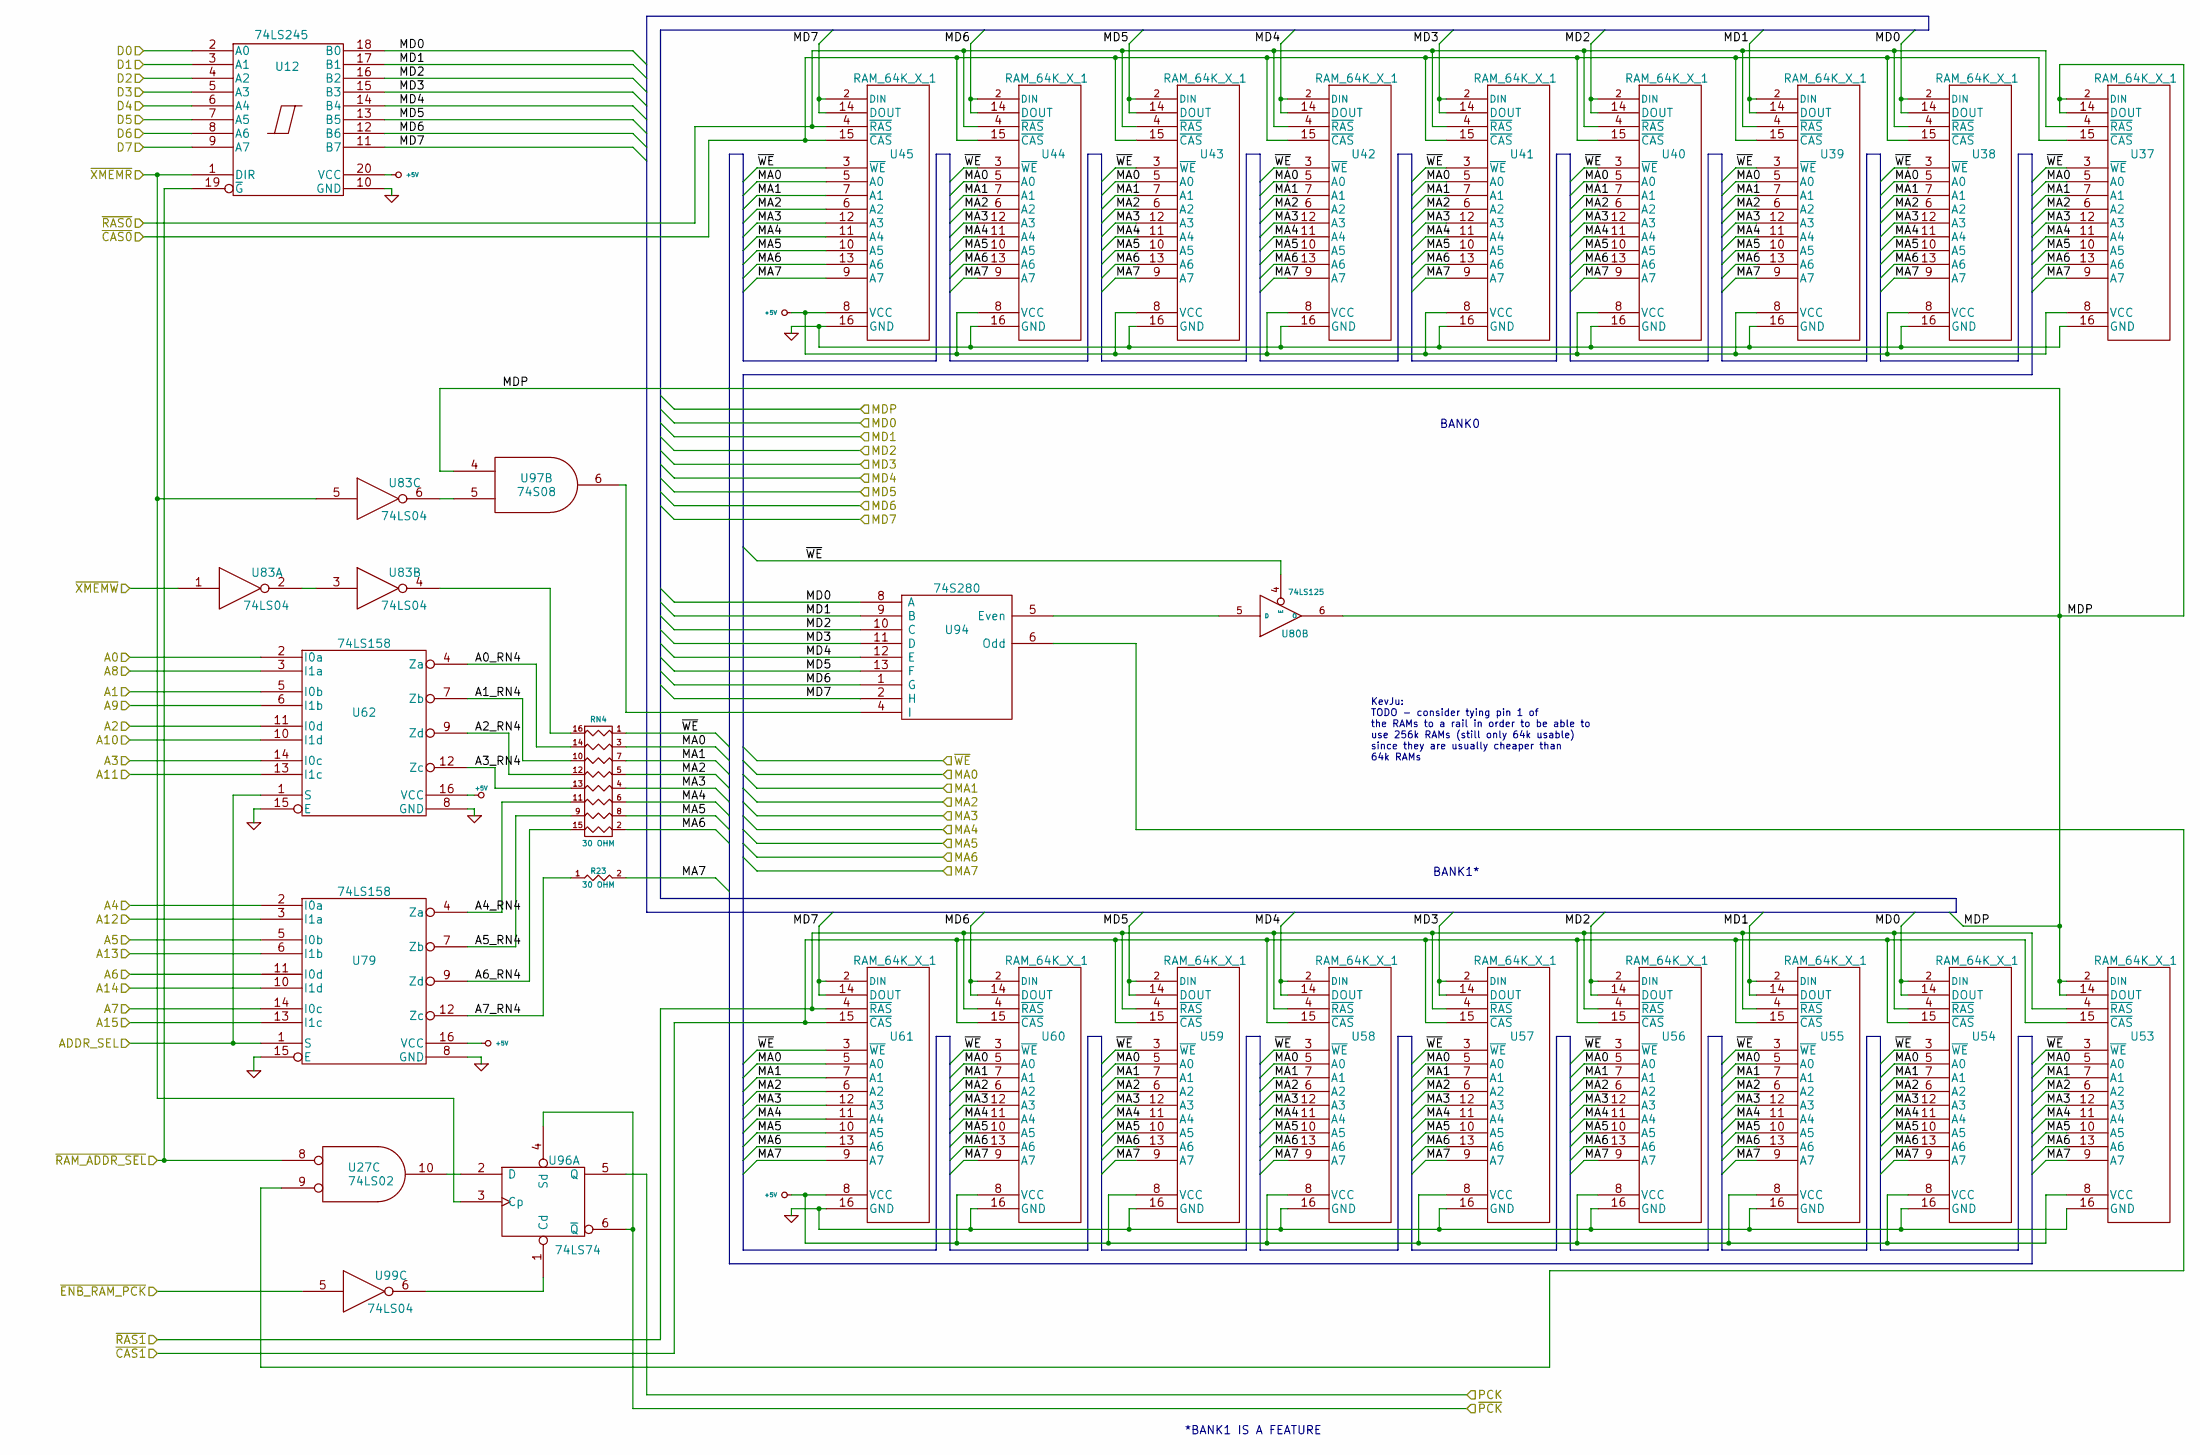
[picture p10: schematic SHEET6.kicad_sch]

Parts:
R23: 30 OHM; R5
RN4: 30 OHM; DIP-16__300
U12: 74LS245; DIP-20__300
U27: 74LS02; DIP-14__300
U37, U38, U39, U40, U41, U42, U43, U44, U45, U53, U54, U55, U56, U57, U58, U59, U60, U61: RAM_64K_X_1; DIP-16__300
U62, U79: 74LS158; DIP-16__300
U80: 74LS125; DIP-14__300
U83, U99: 74LS04; DIP-14__300
U94: 74S280; DIP-14__300
U96: 74LS74; DIP-14__300
U97: 74S08; DIP-14__300

Connections:
+5V: U12.20 (VCC), U37.8 (VCC), U38.8 (VCC), U39.8 (VCC), U40.8 (VCC), U41.8 (VCC), U42.8 (VCC), U43.8 (VCC), U44.8 (VCC), U45.8 (VCC), U53.8 (VCC), U54.8 (VCC), U55.8 (VCC), U56.8 (VCC), U57.8 (VCC), U58.8 (VCC), U59.8 (VCC), U60.8 (VCC), U61.8 (VCC), U62.16 (VCC), U79.16 (VCC)
A0: U62.2 (I0a)
A0_RN4: RN4.14 (R3), U62.4 (Za)
A1: U62.5 (I0b)
A1_RN4: RN4.10 (R7), U62.7 (Zb)
A2: U62.11 (I0d)
A2_RN4: RN4.12 (R5), U62.9 (Zd)
A3: U62.14 (I0c)
A3_RN4: RN4.13 (R4), U62.12 (Zc)
A4: U79.2 (I0a)
A4_RN4: RN4.11 (R6), U79.4 (Za)
A5: U79.5 (I0b)
A5_RN4: RN4.9 (R8), U79.7 (Zb)
A6: U79.11 (I0d)
A6_RN4: RN4.15 (R2), U79.9 (Zd)
A7: U79.14 (I0c)
A7_RN4: R23.1, U79.12 (Zc)
A8: U62.3 (I1a)
A9: U62.6 (I1b)
A10: U62.10 (I1d)
A11: U62.13 (I1c)
A12: U79.3 (I1a)
A13: U79.6 (I1b)
A14: U79.10 (I1d)
A15: U79.13 (I1c)
ADDR_SEL: U62.1 (S), U79.1 (S)
D0: U12.2 (A0)
D1: U12.3 (A1)
D2: U12.4 (A2)
D3: U12.5 (A3)
D4: U12.6 (A4)
D5: U12.7 (A5)
D6: U12.8 (A6)
D7: U12.9 (A7)
GND: U12.10 (GND), U37.16 (GND), U38.16 (GND), U39.16 (GND), U40.16 (GND), U41.16 (GND), U42.16 (GND), U43.16 (GND), U44.16 (GND), U45.16 (GND), U53.16 (GND), U54.16 (GND), U55.16 (GND), U56.16 (GND), U57.16 (GND), U58.16 (GND), U59.16 (GND), U60.16 (GND), U61.16 (GND), U62.8 (GND), U62.15 (E), U79.8 (GND), U79.15 (E)
MA0: RN4.3, U37.5 (A0), U38.5 (A0), U39.5 (A0), U40.5 (A0), U41.5 (A0), U42.5 (A0), U43.5 (A0), U44.5 (A0), U45.5 (A0), U53.5 (A0), U54.5 (A0), U55.5 (A0), U56.5 (A0), U57.5 (A0), U58.5 (A0), U59.5 (A0), U60.5 (A0), U61.5 (A0)
MA1: RN4.7, U37.7 (A1), U38.7 (A1), U39.7 (A1), U40.7 (A1), U41.7 (A1), U42.7 (A1), U43.7 (A1), U44.7 (A1), U45.7 (A1), U53.7 (A1), U54.7 (A1), U55.7 (A1), U56.7 (A1), U57.7 (A1), U58.7 (A1), U59.7 (A1), U60.7 (A1), U61.7 (A1)
MA2: RN4.5, U37.6 (A2), U38.6 (A2), U39.6 (A2), U40.6 (A2), U41.6 (A2), U42.6 (A2), U43.6 (A2), U44.6 (A2), U45.6 (A2), U53.6 (A2), U54.6 (A2), U55.6 (A2), U56.6 (A2), U57.6 (A2), U58.6 (A2), U59.6 (A2), U60.6 (A2), U61.6 (A2)
MA3: RN4.4, U37.12 (A3), U38.12 (A3), U39.12 (A3), U40.12 (A3), U41.12 (A3), U42.12 (A3), U43.12 (A3), U44.12 (A3), U45.12 (A3), U53.12 (A3), U54.12 (A3), U55.12 (A3), U56.12 (A3), U57.12 (A3), U58.12 (A3), U59.12 (A3), U60.12 (A3), U61.12 (A3)
MA4: RN4.6, U37.11 (A4), U38.11 (A4), U39.11 (A4), U40.11 (A4), U41.11 (A4), U42.11 (A4), U43.11 (A4), U44.11 (A4), U45.11 (A4), U53.11 (A4), U54.11 (A4), U55.11 (A4), U56.11 (A4), U57.11 (A4), U58.11 (A4), U59.11 (A4), U60.11 (A4), U61.11 (A4)
MA5: RN4.8, U37.10 (A5), U38.10 (A5), U39.10 (A5), U40.10 (A5), U41.10 (A5), U42.10 (A5), U43.10 (A5), U44.10 (A5), U45.10 (A5), U53.10 (A5), U54.10 (A5), U55.10 (A5), U56.10 (A5), U57.10 (A5), U58.10 (A5), U59.10 (A5), U60.10 (A5), U61.10 (A5)
MA6: RN4.2, U37.13 (A6), U38.13 (A6), U39.13 (A6), U40.13 (A6), U41.13 (A6), U42.13 (A6), U43.13 (A6), U44.13 (A6), U45.13 (A6), U53.13 (A6), U54.13 (A6), U55.13 (A6), U56.13 (A6), U57.13 (A6), U58.13 (A6), U59.13 (A6), U60.13 (A6), U61.13 (A6)
MA7: R23.2, U37.9 (A7), U38.9 (A7), U39.9 (A7), U40.9 (A7), U41.9 (A7), U42.9 (A7), U43.9 (A7), U44.9 (A7), U45.9 (A7), U53.9 (A7), U54.9 (A7), U55.9 (A7), U56.9 (A7), U57.9 (A7), U58.9 (A7), U59.9 (A7), U60.9 (A7), U61.9 (A7)
MD0: U12.18 (B0), U38.2 (DIN), U38.14 (DOUT), U54.2 (DIN), U54.14 (DOUT), U94.8 (A)
MD1: U12.17 (B1), U39.2 (DIN), U39.14 (DOUT), U55.2 (DIN), U55.14 (DOUT), U94.9 (B)
MD2: U12.16 (B2), U40.2 (DIN), U40.14 (DOUT), U56.2 (DIN), U56.14 (DOUT), U94.10 (C)
MD3: U12.15 (B3), U41.2 (DIN), U41.14 (DOUT), U57.2 (DIN), U57.14 (DOUT), U94.11 (D)
MD4: U12.14 (B4), U42.2 (DIN), U42.14 (DOUT), U58.2 (DIN), U58.14 (DOUT), U94.12 (E)
MD5: U12.13 (B5), U43.2 (DIN), U43.14 (DOUT), U59.2 (DIN), U59.14 (DOUT), U94.13 (F)
MD6: U12.12 (B6), U44.2 (DIN), U44.14 (DOUT), U60.2 (DIN), U60.14 (DOUT), U94.1 (G)
MD7: U12.11 (B7), U45.2 (DIN), U45.14 (DOUT), U61.2 (DIN), U61.14 (DOUT), U94.2 (H)
MDP: U37.2 (DIN), U37.14 (DOUT), U53.2 (DIN), U53.14 (DOUT), U80.6 (O), U97.4
unnamed: RN4.16 (R1), U83.4
unnamed: U27.9, U94.6 (Odd)
unnamed: U27.10, U96.2 (D)
unnamed: U80.5 (D), U94.5 (Even)
unnamed: U83.2, U83.3
unnamed: U83.6, U97.5
unnamed: U94.4 (I), U97.6
unnamed: U96.1 (Cd), U99.6
PCK: U96.5 (Q)
~CAS0: U37.15 (~CAS), U38.15 (~CAS), U39.15 (~CAS), U40.15 (~CAS), U41.15 (~CAS), U42.15 (~CAS), U43.15 (~CAS), U44.15 (~CAS), U45.15 (~CAS)
~CAS1: U53.15 (~CAS), U54.15 (~CAS), U55.15 (~CAS), U56.15 (~CAS), U57.15 (~CAS), U58.15 (~CAS), U59.15 (~CAS), U60.15 (~CAS), U61.15 (~CAS)
~ENB_RAM_PCK: U99.5
~PCK: U96.4 (Sd), U96.6 (~Q)
~RAM_ADDR_SEL: U12.19 (~G), U27.8
~RAS0: U37.4 (~RAS), U38.4 (~RAS), U39.4 (~RAS), U40.4 (~RAS), U41.4 (~RAS), U42.4 (~RAS), U43.4 (~RAS), U44.4 (~RAS), U45.4 (~RAS)
~RAS1: U53.4 (~RAS), U54.4 (~RAS), U55.4 (~RAS), U56.4 (~RAS), U57.4 (~RAS), U58.4 (~RAS), U59.4 (~RAS), U60.4 (~RAS), U61.4 (~RAS)
~WE: RN4.1, U37.3 (~WE), U38.3 (~WE), U39.3 (~WE), U40.3 (~WE), U41.3 (~WE), U42.3 (~WE), U43.3 (~WE), U44.3 (~WE), U45.3 (~WE), U53.3 (~WE), U54.3 (~WE), U55.3 (~WE), U56.3 (~WE), U57.3 (~WE), U58.3 (~WE), U59.3 (~WE), U60.3 (~WE), U61.3 (~WE), U80.4 (E)
~XMEMR: U12.1 (DIR), U83.5, U96.3 (Cp)
~XMEMW: U83.1

Notes on the sheet:
*BANK1 IS A FEATURE
KevJu: TODO - consider tying pin 1 of the RAMs to a rail in order to be able to use 256k RAMs (still only 64k usable) since they are usually cheaper than 64k RAMs
BANK0
BANK1*
