kev-ju/PC-Retro-MTM/SHEET7.kicad_sch

## KiCad design SHEET7.kicad_sch (2026-03-31)

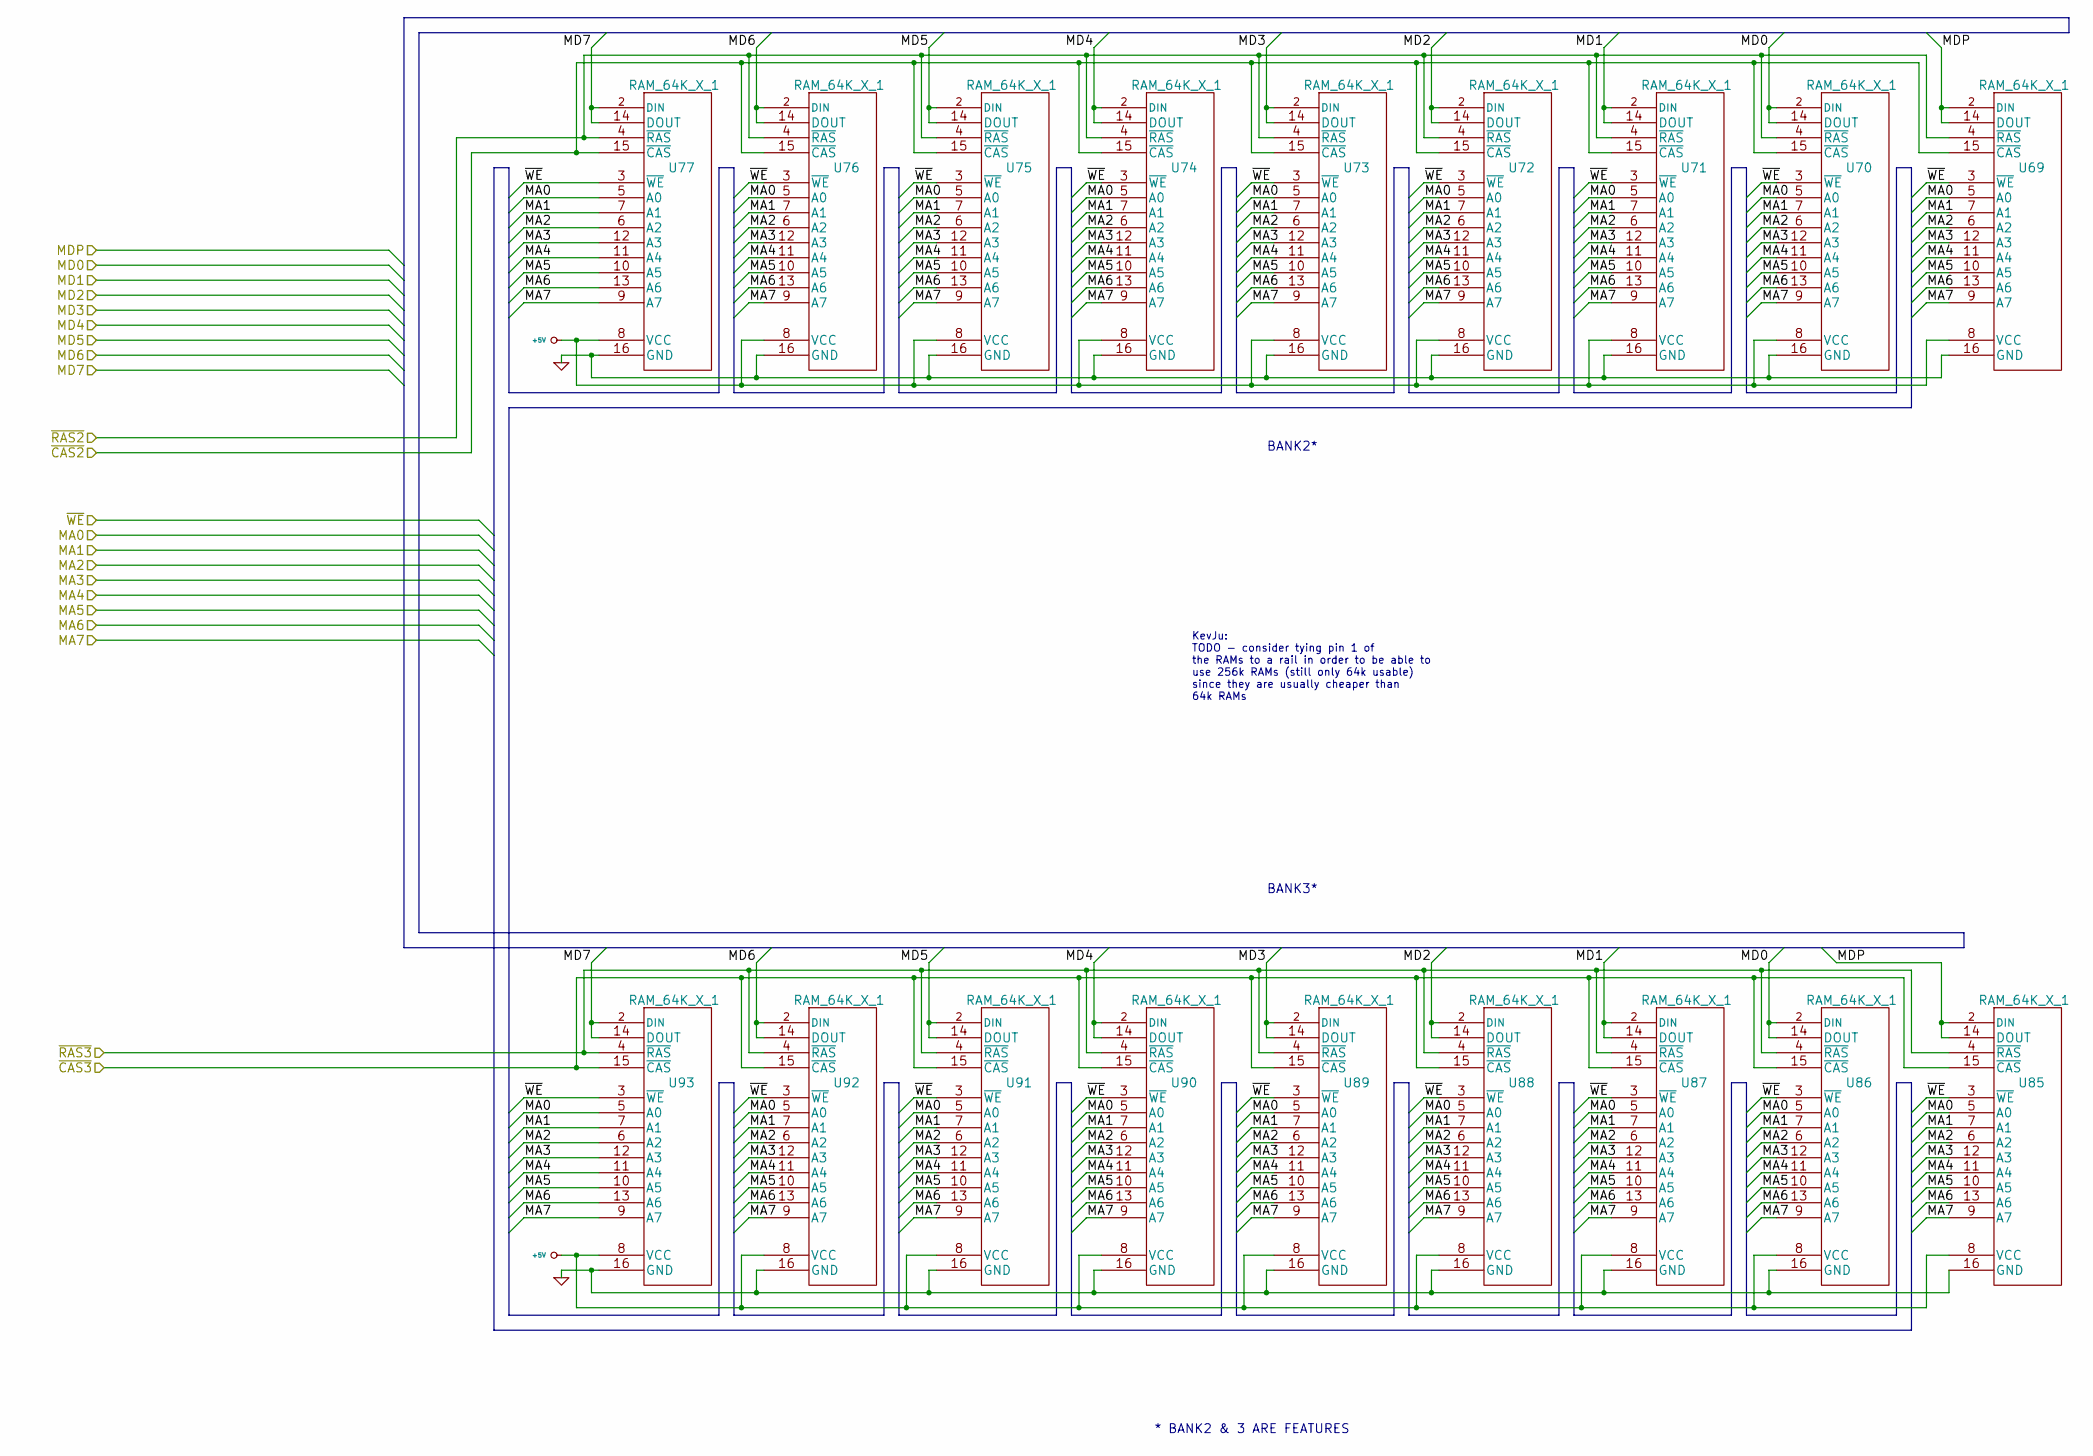
[picture p11: schematic SHEET7.kicad_sch]

Parts:
U69, U70, U71, U72, U73, U74, U75, U76, U77, U85, U86, U87, U88, U89, U90, U91, U92, U93: RAM_64K_X_1; DIP-16__300

Connections:
+5V: U69.8 (VCC), U70.8 (VCC), U71.8 (VCC), U72.8 (VCC), U73.8 (VCC), U74.8 (VCC), U75.8 (VCC), U76.8 (VCC), U77.8 (VCC), U85.8 (VCC), U86.8 (VCC), U87.8 (VCC), U88.8 (VCC), U89.8 (VCC), U90.8 (VCC), U91.8 (VCC), U92.8 (VCC), U93.8 (VCC)
GND: U69.16 (GND), U70.16 (GND), U71.16 (GND), U72.16 (GND), U73.16 (GND), U74.16 (GND), U75.16 (GND), U76.16 (GND), U77.16 (GND), U85.16 (GND), U86.16 (GND), U87.16 (GND), U88.16 (GND), U89.16 (GND), U90.16 (GND), U91.16 (GND), U92.16 (GND), U93.16 (GND)
MA0: U69.5 (A0), U70.5 (A0), U71.5 (A0), U72.5 (A0), U73.5 (A0), U74.5 (A0), U75.5 (A0), U76.5 (A0), U77.5 (A0), U85.5 (A0), U86.5 (A0), U87.5 (A0), U88.5 (A0), U89.5 (A0), U90.5 (A0), U91.5 (A0), U92.5 (A0), U93.5 (A0)
MA1: U69.7 (A1), U70.7 (A1), U71.7 (A1), U72.7 (A1), U73.7 (A1), U74.7 (A1), U75.7 (A1), U76.7 (A1), U77.7 (A1), U85.7 (A1), U86.7 (A1), U87.7 (A1), U88.7 (A1), U89.7 (A1), U90.7 (A1), U91.7 (A1), U92.7 (A1), U93.7 (A1)
MA2: U69.6 (A2), U70.6 (A2), U71.6 (A2), U72.6 (A2), U73.6 (A2), U74.6 (A2), U75.6 (A2), U76.6 (A2), U77.6 (A2), U85.6 (A2), U86.6 (A2), U87.6 (A2), U88.6 (A2), U89.6 (A2), U90.6 (A2), U91.6 (A2), U92.6 (A2), U93.6 (A2)
MA3: U69.12 (A3), U70.12 (A3), U71.12 (A3), U72.12 (A3), U73.12 (A3), U74.12 (A3), U75.12 (A3), U76.12 (A3), U77.12 (A3), U85.12 (A3), U86.12 (A3), U87.12 (A3), U88.12 (A3), U89.12 (A3), U90.12 (A3), U91.12 (A3), U92.12 (A3), U93.12 (A3)
MA4: U69.11 (A4), U70.11 (A4), U71.11 (A4), U72.11 (A4), U73.11 (A4), U74.11 (A4), U75.11 (A4), U76.11 (A4), U77.11 (A4), U85.11 (A4), U86.11 (A4), U87.11 (A4), U88.11 (A4), U89.11 (A4), U90.11 (A4), U91.11 (A4), U92.11 (A4), U93.11 (A4)
MA5: U69.10 (A5), U70.10 (A5), U71.10 (A5), U72.10 (A5), U73.10 (A5), U74.10 (A5), U75.10 (A5), U76.10 (A5), U77.10 (A5), U85.10 (A5), U86.10 (A5), U87.10 (A5), U88.10 (A5), U89.10 (A5), U90.10 (A5), U91.10 (A5), U92.10 (A5), U93.10 (A5)
MA6: U69.13 (A6), U70.13 (A6), U71.13 (A6), U72.13 (A6), U73.13 (A6), U74.13 (A6), U75.13 (A6), U76.13 (A6), U77.13 (A6), U85.13 (A6), U86.13 (A6), U87.13 (A6), U88.13 (A6), U89.13 (A6), U90.13 (A6), U91.13 (A6), U92.13 (A6), U93.13 (A6)
MA7: U69.9 (A7), U70.9 (A7), U71.9 (A7), U72.9 (A7), U73.9 (A7), U74.9 (A7), U75.9 (A7), U76.9 (A7), U77.9 (A7), U85.9 (A7), U86.9 (A7), U87.9 (A7), U88.9 (A7), U89.9 (A7), U90.9 (A7), U91.9 (A7), U92.9 (A7), U93.9 (A7)
MD0: U70.2 (DIN), U70.14 (DOUT), U86.2 (DIN), U86.14 (DOUT)
MD1: U71.2 (DIN), U71.14 (DOUT), U87.2 (DIN), U87.14 (DOUT)
MD2: U72.2 (DIN), U72.14 (DOUT), U88.2 (DIN), U88.14 (DOUT)
MD3: U73.2 (DIN), U73.14 (DOUT), U89.2 (DIN), U89.14 (DOUT)
MD4: U74.2 (DIN), U74.14 (DOUT), U90.2 (DIN), U90.14 (DOUT)
MD5: U75.2 (DIN), U75.14 (DOUT), U91.2 (DIN), U91.14 (DOUT)
MD6: U76.2 (DIN), U76.14 (DOUT), U92.2 (DIN), U92.14 (DOUT)
MD7: U77.2 (DIN), U77.14 (DOUT), U93.2 (DIN), U93.14 (DOUT)
MDP: U69.2 (DIN), U69.14 (DOUT), U85.2 (DIN), U85.14 (DOUT)
~CAS2: U69.15 (~CAS), U70.15 (~CAS), U71.15 (~CAS), U72.15 (~CAS), U73.15 (~CAS), U74.15 (~CAS), U75.15 (~CAS), U76.15 (~CAS), U77.15 (~CAS)
~CAS3: U85.15 (~CAS), U86.15 (~CAS), U87.15 (~CAS), U88.15 (~CAS), U89.15 (~CAS), U90.15 (~CAS), U91.15 (~CAS), U92.15 (~CAS), U93.15 (~CAS)
~RAS2: U69.4 (~RAS), U70.4 (~RAS), U71.4 (~RAS), U72.4 (~RAS), U73.4 (~RAS), U74.4 (~RAS), U75.4 (~RAS), U76.4 (~RAS), U77.4 (~RAS)
~RAS3: U85.4 (~RAS), U86.4 (~RAS), U87.4 (~RAS), U88.4 (~RAS), U89.4 (~RAS), U90.4 (~RAS), U91.4 (~RAS), U92.4 (~RAS), U93.4 (~RAS)
~WE: U69.3 (~WE), U70.3 (~WE), U71.3 (~WE), U72.3 (~WE), U73.3 (~WE), U74.3 (~WE), U75.3 (~WE), U76.3 (~WE), U77.3 (~WE), U85.3 (~WE), U86.3 (~WE), U87.3 (~WE), U88.3 (~WE), U89.3 (~WE), U90.3 (~WE), U91.3 (~WE), U92.3 (~WE), U93.3 (~WE)

Notes on the sheet:
KevJu: TODO - consider tying pin 1 of the RAMs to a rail in order to be able to use 256k RAMs (still only 64k usable) since they are usually cheaper than 64k RAMs
BANK3*
BANK2*
* BANK2 & 3 ARE FEATURES
