kev-ju/PC-Retro-MTM/SHEET8.kicad_sch

## KiCad design SHEET8.kicad_sch (2026-03-31)

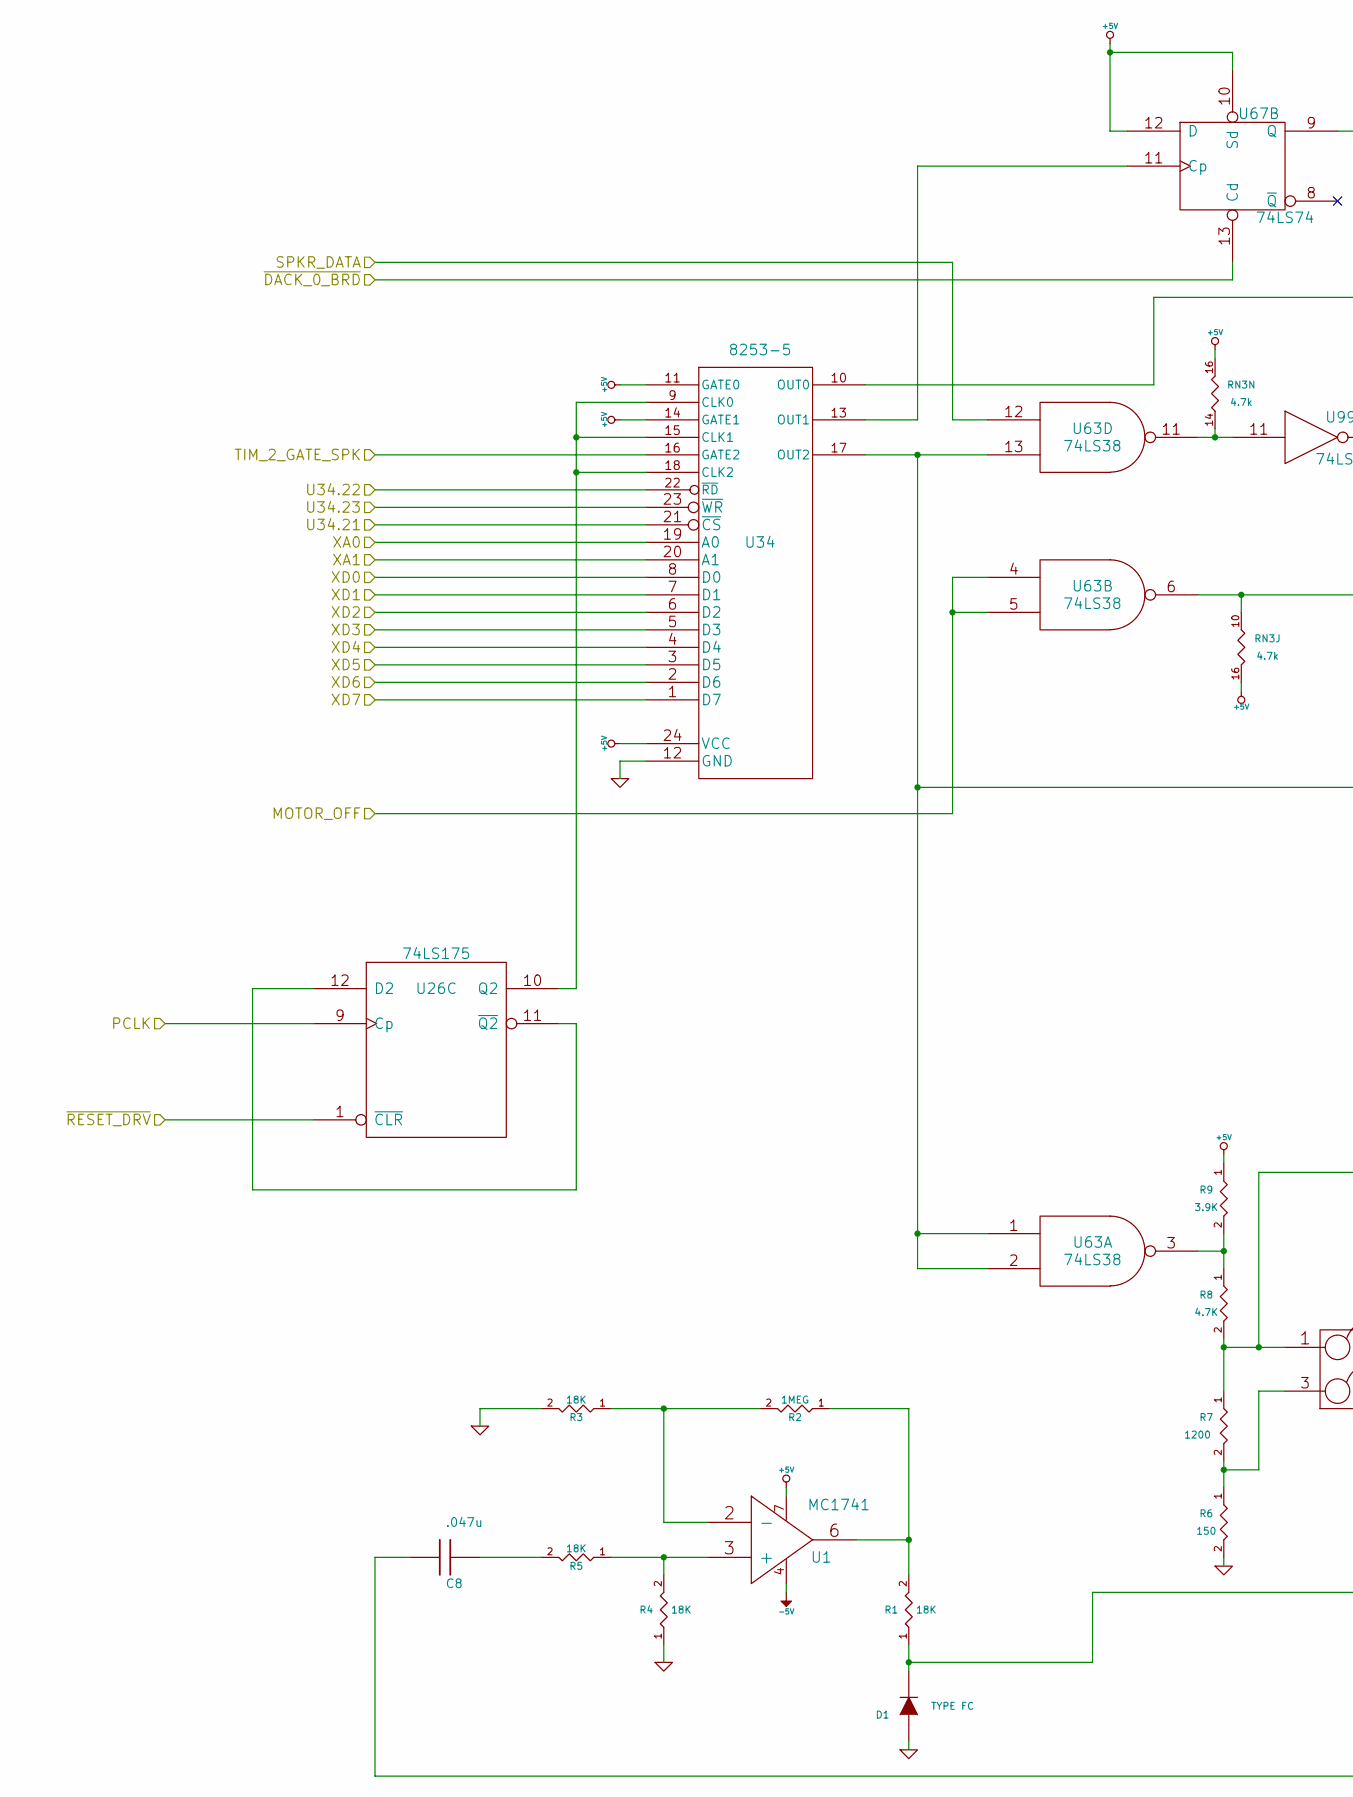
[picture p12: schematic SHEET8.kicad_sch, part in row 1, column 1]

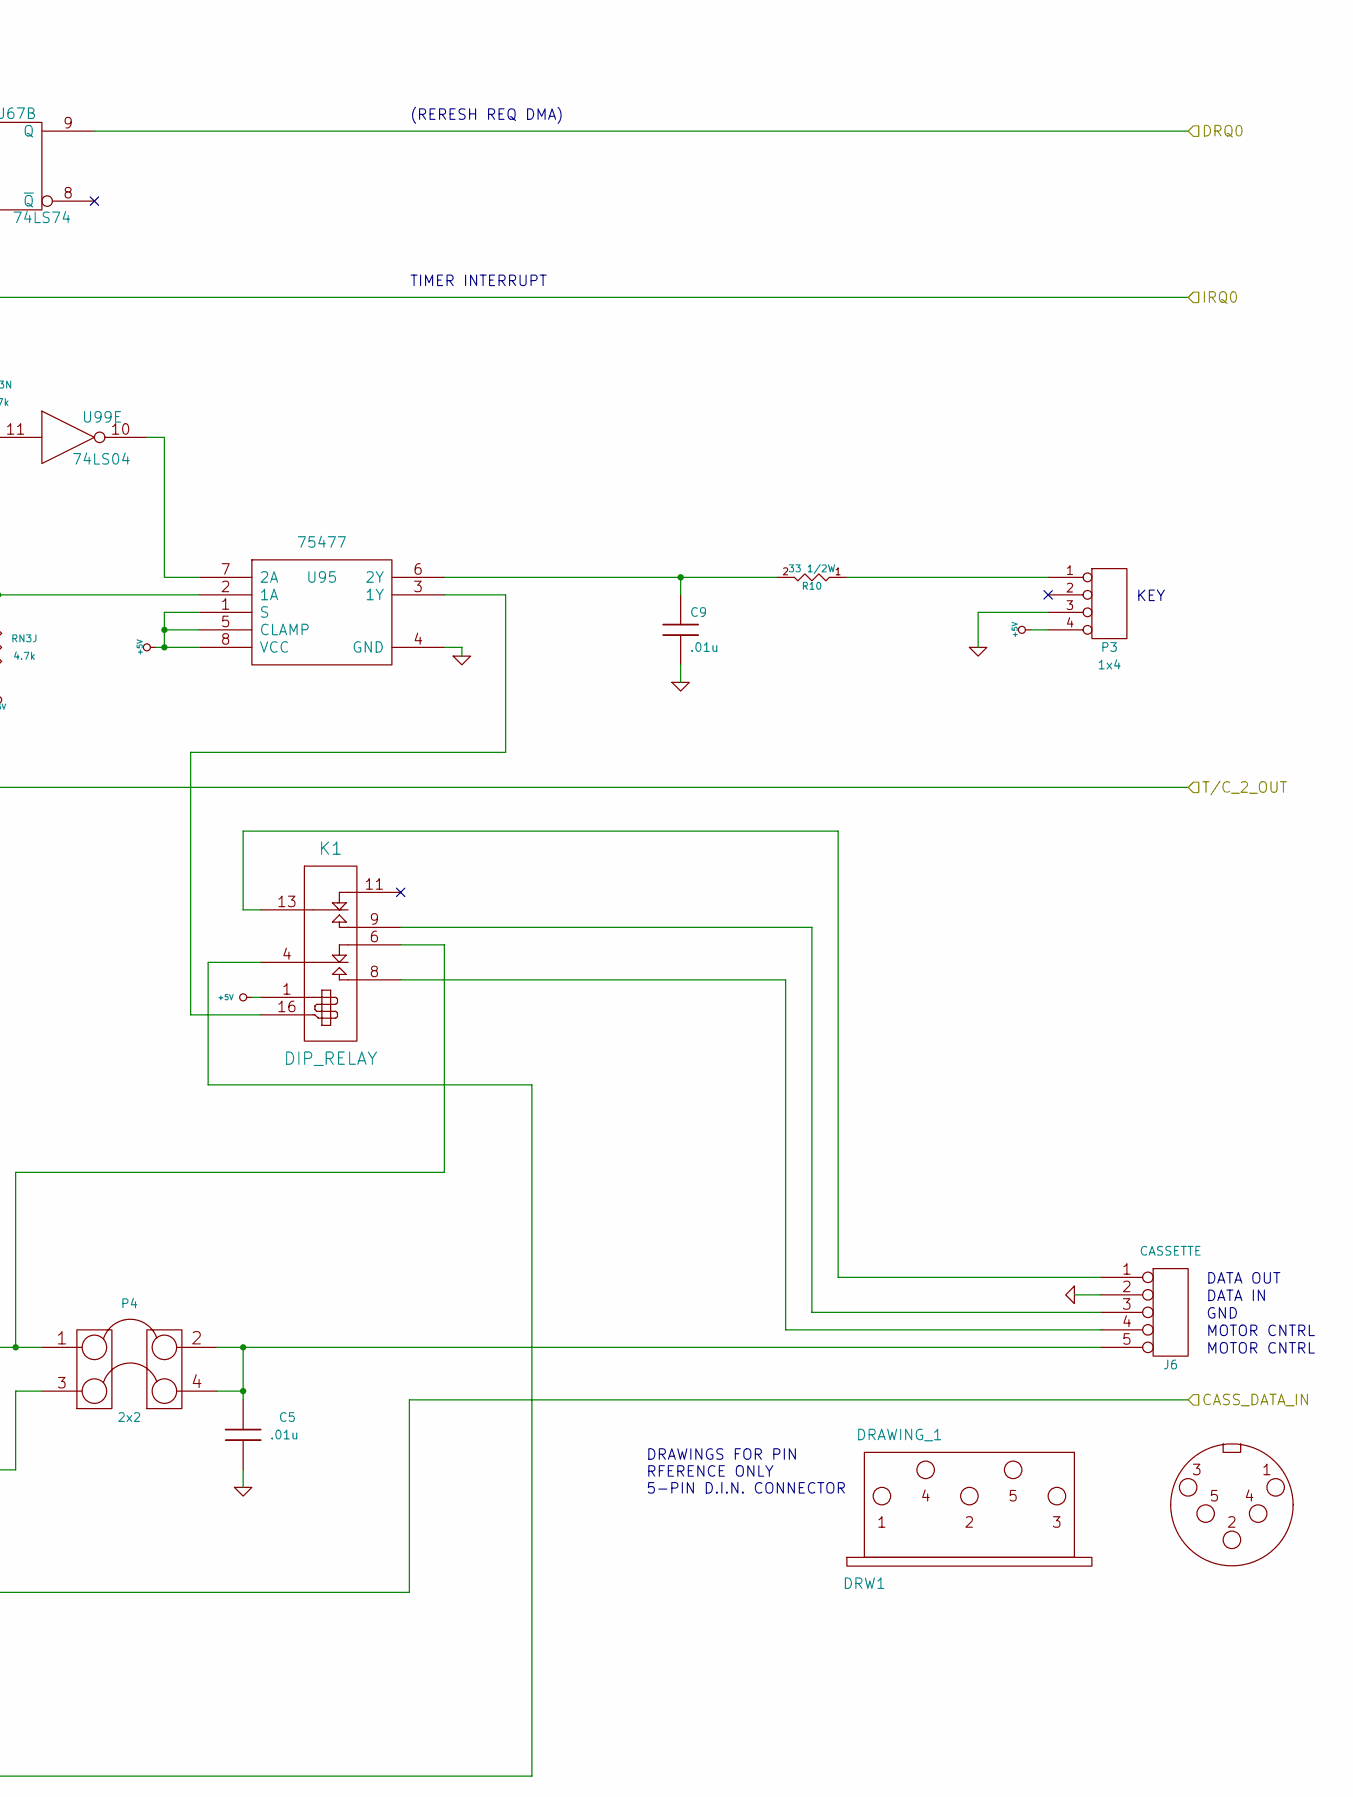
[picture p13: schematic SHEET8.kicad_sch, part in row 1, column 2]

Parts:
C5, C9: .01u; CP8
C8: .047u; CP8
D1: TYPE FC; D5
DRW1: DRAWING_1
J6: CASSETTE; 5PINDIN
K1: DIP_RELAY; G5V-2DPDT
P3: 1x4; PIN_ARRAY_4x1
P4: 2x2; PIN_ARRAY_2X2
R1, R3, R4, R5: 18K; R5
R2: 1MEG; R5
R6: 150; R5
R7: 1200; R5
R8: 4.7K; R5
R9: 3.9K; R5
R10: 33 1/2W; R5
RN3: 4.7k; DIP-16__300
U1: MC1741; DIP-8__300
U26: 74LS175; DIP-16__300
U34: 8253-5; DIP-24__600
U63: 74LS38; DIP-14__300
U67: 74LS74; DIP-14__300
U95: 75477; DIP-8__300
U99: 74LS04; DIP-14__300

Connections:
+5V: K1.1, P3.4, R9.1, RN3.16, U1.7, U34.11 (GATE0), U34.14 (GATE1), U34.24 (VCC), U67.10 (Sd), U67.12 (D), U95.1 (S), U95.5 (CLAMP), U95.8 (VCC)
-5V: U1.4
CASS_DATA_IN: D1.2 (K), R1.1
DRQ0: U67.9 (Q)
GND: C5.2, C9.2, D1.1 (A), J6.2, P3.3, R3.2, R4.1, R6.2, U34.12 (GND), U95.4 (GND)
IRQ0: U34.10 (OUT0)
MOTOR_OFF: U63.4, U63.5
unnamed: C5.1, J6.5, P4.2, P4.4
unnamed: C8.1, R5.2
unnamed: C8.2, K1.4 (C1)
unnamed: C9.1, R10.2, U95.6 (2Y)
unnamed: J6.1, K1.13 (C2)
unnamed: J6.3, K1.9 (T2)
unnamed: J6.4, K1.8 (T1)
unnamed: K1.6 (R1), P4.1, R7.1, R8.2
unnamed: K1.16, U95.3 (1Y)
unnamed: P3.1, R10.1
unnamed: P4.3, R6.1, R7.2
unnamed: R1.2, R2.1, U1.6
unnamed: R2.2, R3.1, U1.2 (-)
unnamed: R4.2, R5.1, U1.3 (+)
unnamed: R8.1, R9.2, U63.3
unnamed: RN3.10 (P15), U63.6, U95.2 (1A)
unnamed: RN3.14 (P15), U63.11, U99.11
unnamed: U26.10 (Q2), U34.9 (CLK0), U34.15 (CLK1), U34.18 (CLK2)
unnamed: U26.11 (~Q2), U26.12 (D2)
unnamed: U34.13 (OUT1), U67.11 (Cp)
unnamed: U95.7 (2A), U99.10
PCLK: U26.9 (Cp)
SPKR_DATA: U63.12
T/C_2_OUT: U34.17 (OUT2), U63.1, U63.2, U63.13
TIM_2_GATE_SPK: U34.16 (GATE2)
U34.21: U34.21 (~CS)
U34.22: U34.22 (~RD)
U34.23: U34.23 (~WR)
XA0: U34.19 (A0)
XA1: U34.20 (A1)
XD0: U34.8 (D0)
XD1: U34.7 (D1)
XD2: U34.6 (D2)
XD3: U34.5 (D3)
XD4: U34.4 (D4)
XD5: U34.3 (D5)
XD6: U34.2 (D6)
XD7: U34.1 (D7)
~DACK_0_BRD: U67.13 (Cd)
~RESET_DRV: U26.1 (~CLR)

Notes on the sheet:
DRAWINGS FOR PIN RFERENCE ONLY 5-PIN D.I.N. CONNECTOR
MOTOR CNTRL
(RERESH REQ DMA)
DATA OUT
GND
TIMER INTERRUPT
KEY
DATA IN
