kev-ju/PC-Retro-MTM/SHEET9.kicad_sch

## KiCad design SHEET9.kicad_sch (2026-03-31)

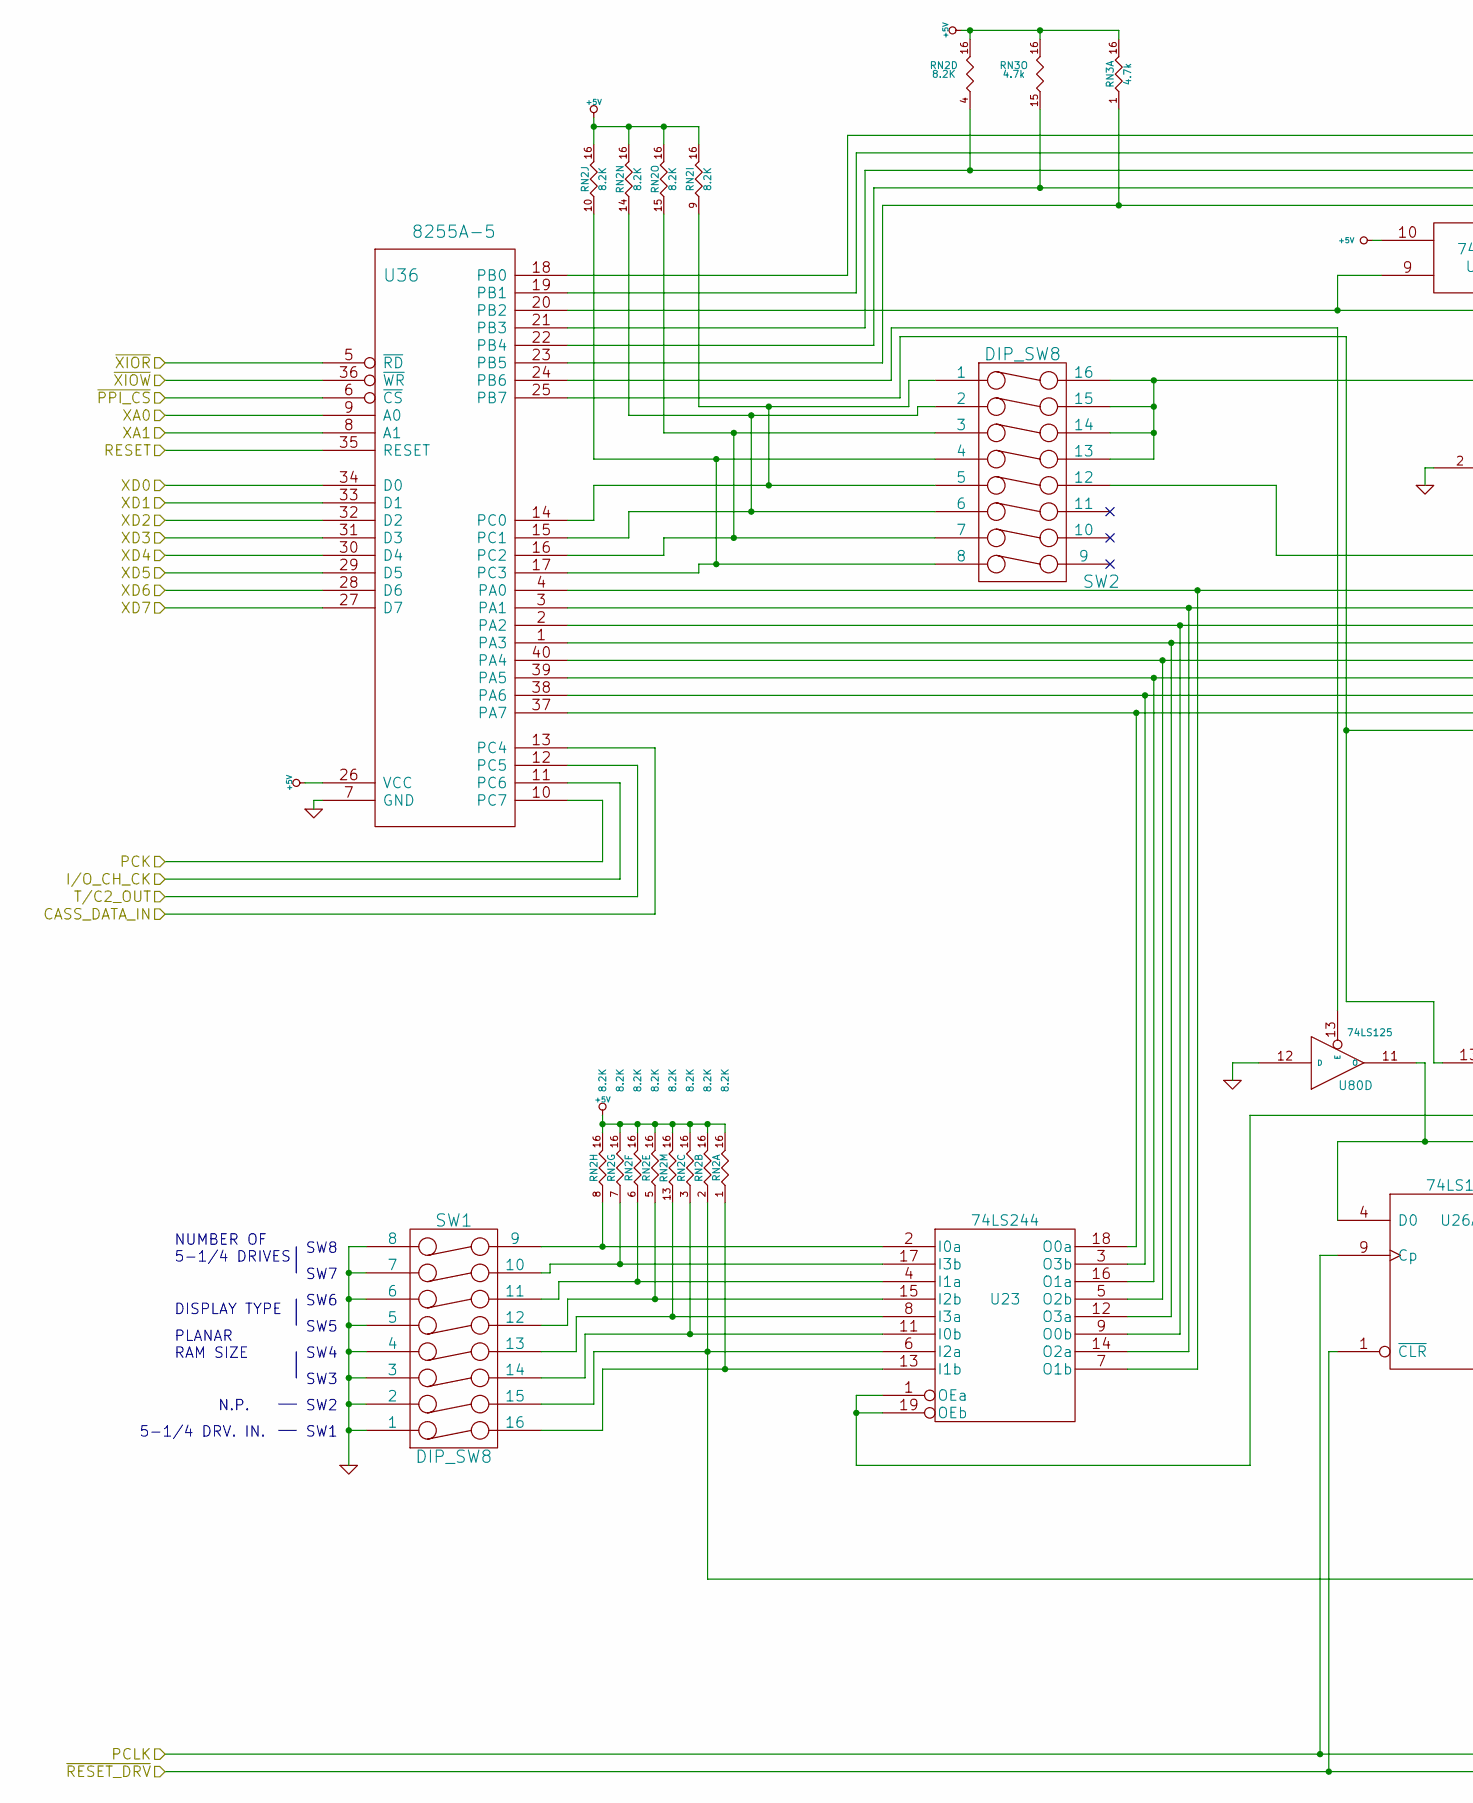
[picture p14: schematic SHEET9.kicad_sch, part in row 1, column 1]

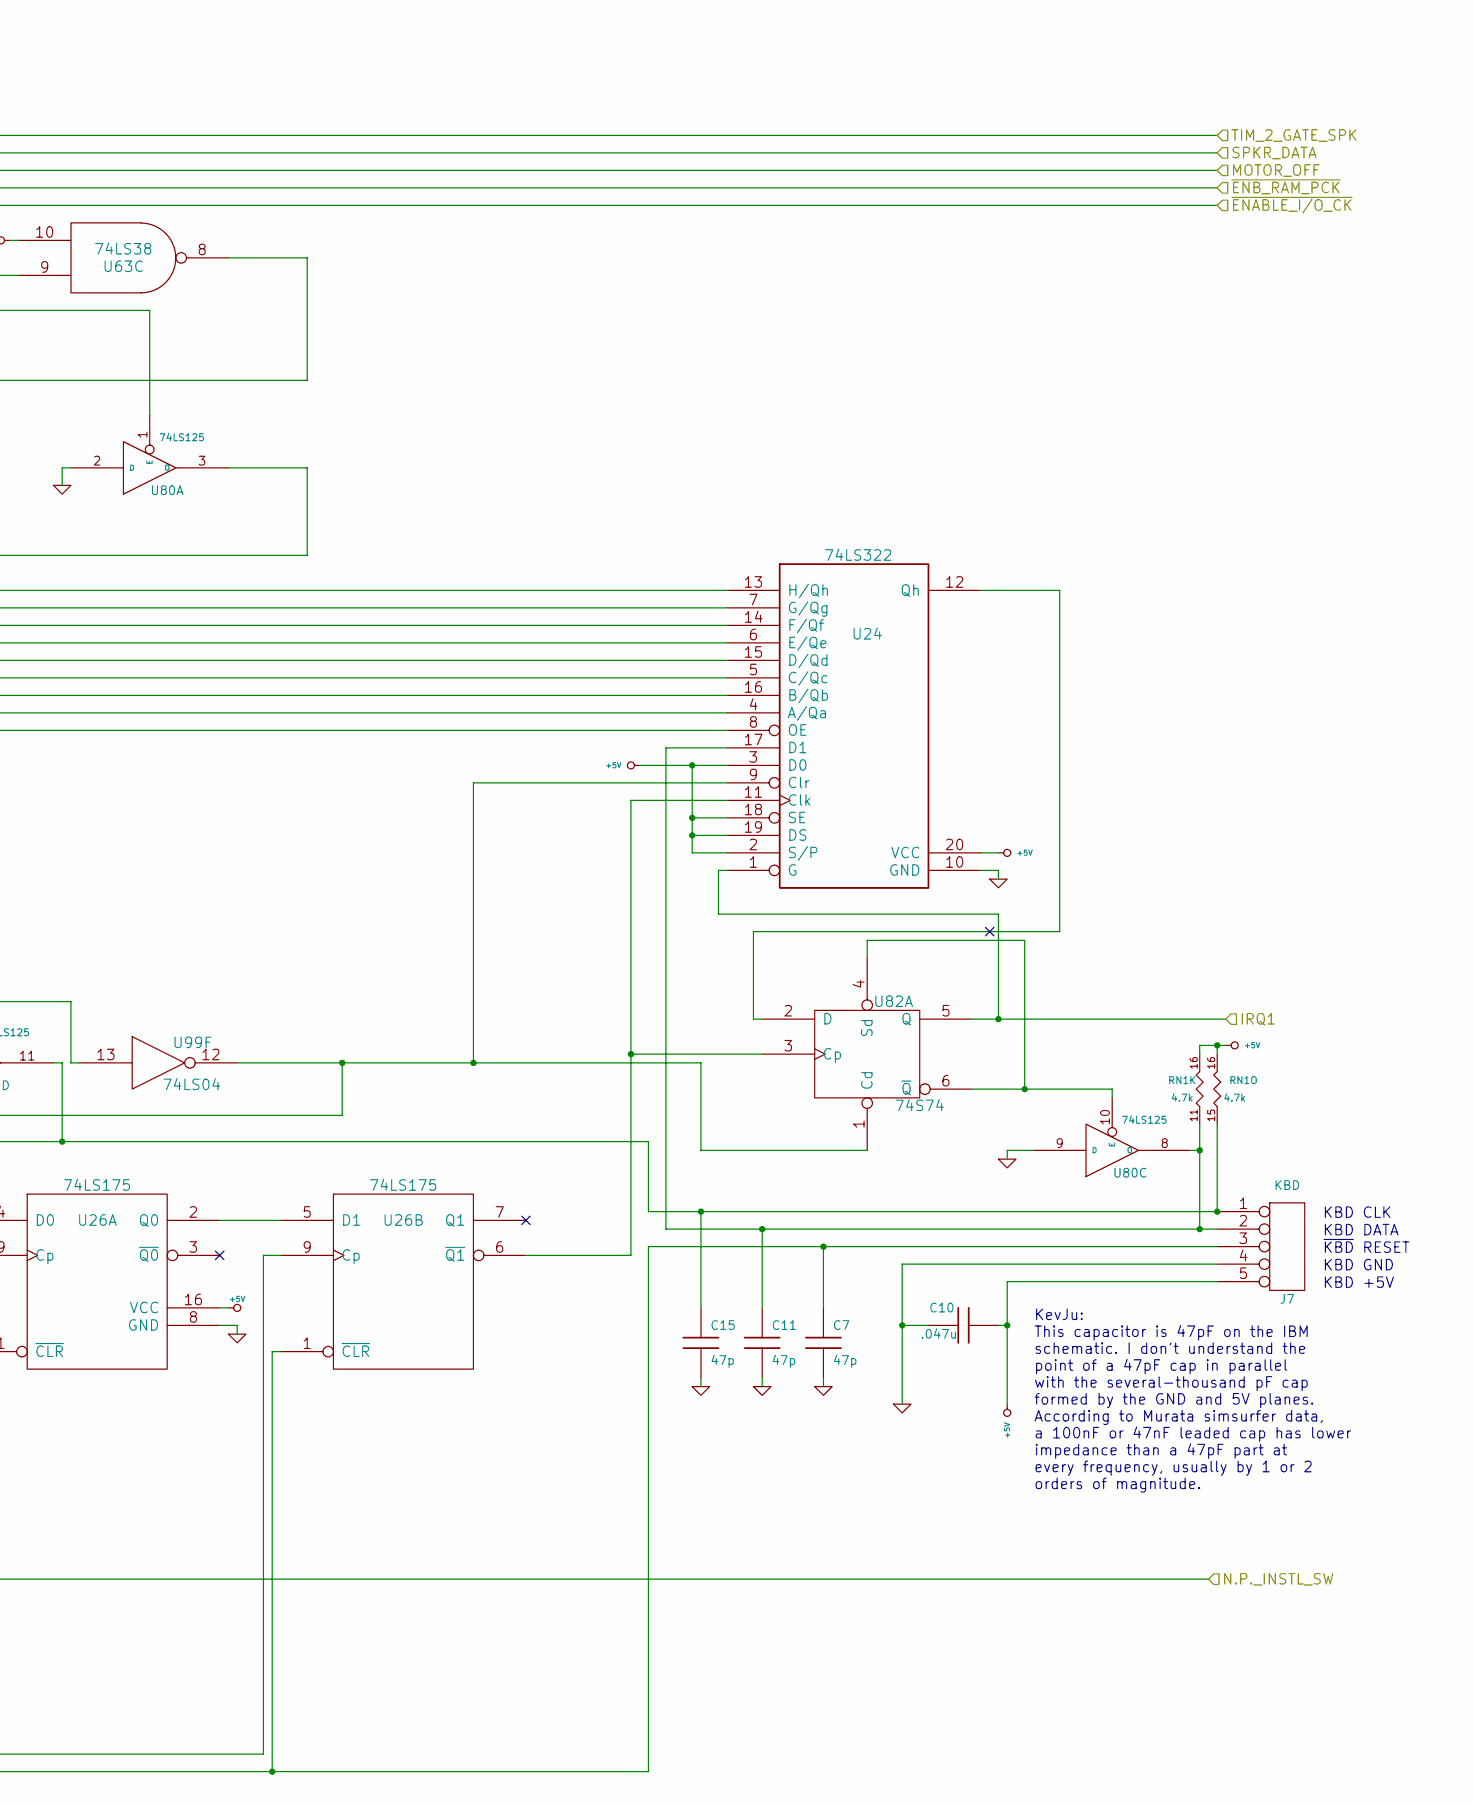
[picture p15: schematic SHEET9.kicad_sch, part in row 1, column 2]

Parts:
C7, C11, C15: 47p; C_254_508_2PIN
C10: .047u; C_254_508_2PIN
J7: KBD; 5PINDIN
RN1, RN3: 4.7k; DIP-16__300
RN2: 8.2K; DIP-16__300
SW1, SW2: DIP_SW8; DIP-16__300
U23: 74LS244; DIP-20__300
U24: 74LS322; DIP-20__300
U26: 74LS175; DIP-16__300
U36: 8255A-5; DIP-40__600
U63: 74LS38; DIP-14__300
U80: 74LS125; DIP-14__300
U82: 74S74; DIP-14__300
U99: 74LS04; DIP-14__300

Connections:
+5V: C10.1, J7.5, RN1.16, RN2.16, RN3.16, U24.2 (S/P), U24.3 (D0), U24.18 (SE), U24.19 (DS), U24.20 (VCC), U26.16 (VCC), U36.26 (VCC), U63.10
CASS_DATA_IN: U36.13 (PC4)
GND: C7.2, C10.2, C11.2, C15.2, J7.4, SW1.1, SW1.2, SW1.3, SW1.4, SW1.5, SW1.6, SW1.7, SW1.8, U24.10 (GND), U26.8 (GND), U36.7 (GND), U80.2 (D), U80.9 (D), U80.12 (D)
I/O_CH_CK: U36.11 (PC6)
IRQ1: U24.1 (G), U82.5 (Q)
MOTOR_OFF: RN2.4 (P15), U36.21 (PB3)
N.P._INSTL_SW: RN2.2 (P15), SW1.15, U23.6 (I2a)
unnamed: C11.1, J7.2, RN1.11 (P15), U24.17 (D1), U80.8 (O)
unnamed: C15.1, J7.1, RN1.15, U26.4 (D0), U80.11 (O)
unnamed: RN2.1 (P15), SW1.16, U23.13 (I1b)
unnamed: RN2.3 (P15), SW1.14, U23.11 (I0b)
unnamed: RN2.5 (P15), SW1.12, U23.15 (I2b)
unnamed: RN2.6 (P15), SW1.11, U23.4 (I1a)
unnamed: RN2.7 (P15), SW1.10, U23.17 (I3b)
unnamed: RN2.8 (P15), SW1.9, U23.2 (I0a)
unnamed: RN2.9 (P15), SW2.1, SW2.5, U36.14 (PC0)
unnamed: RN2.10 (P15), SW2.4, SW2.8, U36.17 (PC3)
unnamed: RN2.13 (P15), SW1.13, U23.8 (I3a)
unnamed: RN2.14 (P15), SW2.2, SW2.6, U36.15 (PC1)
unnamed: RN2.15, SW2.3, SW2.7, U36.16 (PC2)
unnamed: SW2.12, U80.3 (O)
unnamed: SW2.13, SW2.14, SW2.15, SW2.16, U63.8
unnamed: U23.1 (OEa), U23.19 (OEb), U24.9 (Clr), U82.1 (Cd), U99.12
unnamed: U23.3 (O3b), U24.16 (B/Qb), U36.38 (PA6)
unnamed: U23.5 (O2b), U24.15 (D/Qd), U36.40 (PA4)
unnamed: U23.7 (O1b), U24.13 (H/Qh), U36.4 (PA0)
unnamed: U23.9 (O0b), U24.14 (F/Qf), U36.2 (PA2)
unnamed: U23.12 (O3a), U24.6 (E/Qe), U36.1 (PA3)
unnamed: U23.14 (O2a), U24.7 (G/Qg), U36.3 (PA1)
unnamed: U23.16 (O1a), U24.5 (C/Qc), U36.39 (PA5)
unnamed: U23.18 (O0a), U24.4 (A/Qa), U36.37 (PA7)
unnamed: U24.8 (OE), U36.25 (PB7), U99.13
unnamed: U24.11 (Clk), U26.6 (~Q1), U82.3 (Cp)
unnamed: U24.12 (Qh), U82.2 (D)
unnamed: U26.2 (Q0), U26.5 (D1)
unnamed: U36.20 (PB2), U63.9, U80.1 (E)
unnamed: U36.24 (PB6), U80.13 (E)
unnamed: U80.10 (E), U82.4 (Sd), U82.6 (~Q)
PCK: U36.10 (PC7)
PCLK: U26.9 (Cp)
RESET: U36.35 (RESET)
SPKR_DATA: U36.19 (PB1)
T/C2_OUT: U36.12 (PC5)
TIM_2_GATE_SPK: U36.18 (PB0)
XA0: U36.9 (A0)
XA1: U36.8 (A1)
XD0: U36.34 (D0)
XD1: U36.33 (D1)
XD2: U36.32 (D2)
XD3: U36.31 (D3)
XD4: U36.30 (D4)
XD5: U36.29 (D5)
XD6: U36.28 (D6)
XD7: U36.27 (D7)
~ENABLE_I/O_CK: RN3.1 (P15), U36.23 (PB5)
~ENB_RAM_PCK: RN3.15, U36.22 (PB4)
~PPI_CS: U36.6 (~CS)
~RESET_DRV: C7.1, J7.3, U26.1 (~CLR)
~XIOR: U36.5 (~RD)
~XIOW: U36.36 (~WR)

Notes on the sheet:
SW8
KBD CLK
SW7
KevJu: This capacitor is 47pF on the IBM schematic. I don't understand the point of a 47pF cap in parallel with the several-thousand pF cap formed by the GND and 5V planes. According to Murata simsurfer data, a 100nF or 47nF leaded cap has lower impedance than a 47pF part at every frequency, usuall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
SW5
PLANAR RAM SIZE
SW1
DISPLAY TYPE
SW2
SW6
N.P.
NUMBER OF 5-1/4 DRIVES
5-1/4 DRV. IN.
KBD GND
KBD +5V
SW3
~{KBD} RESET
KBD DATA
SW4
