kev-ju/PC-Retro-MTM/SHEET10.kicad_sch

## KiCad design SHEET10.kicad_sch (2026-03-31)

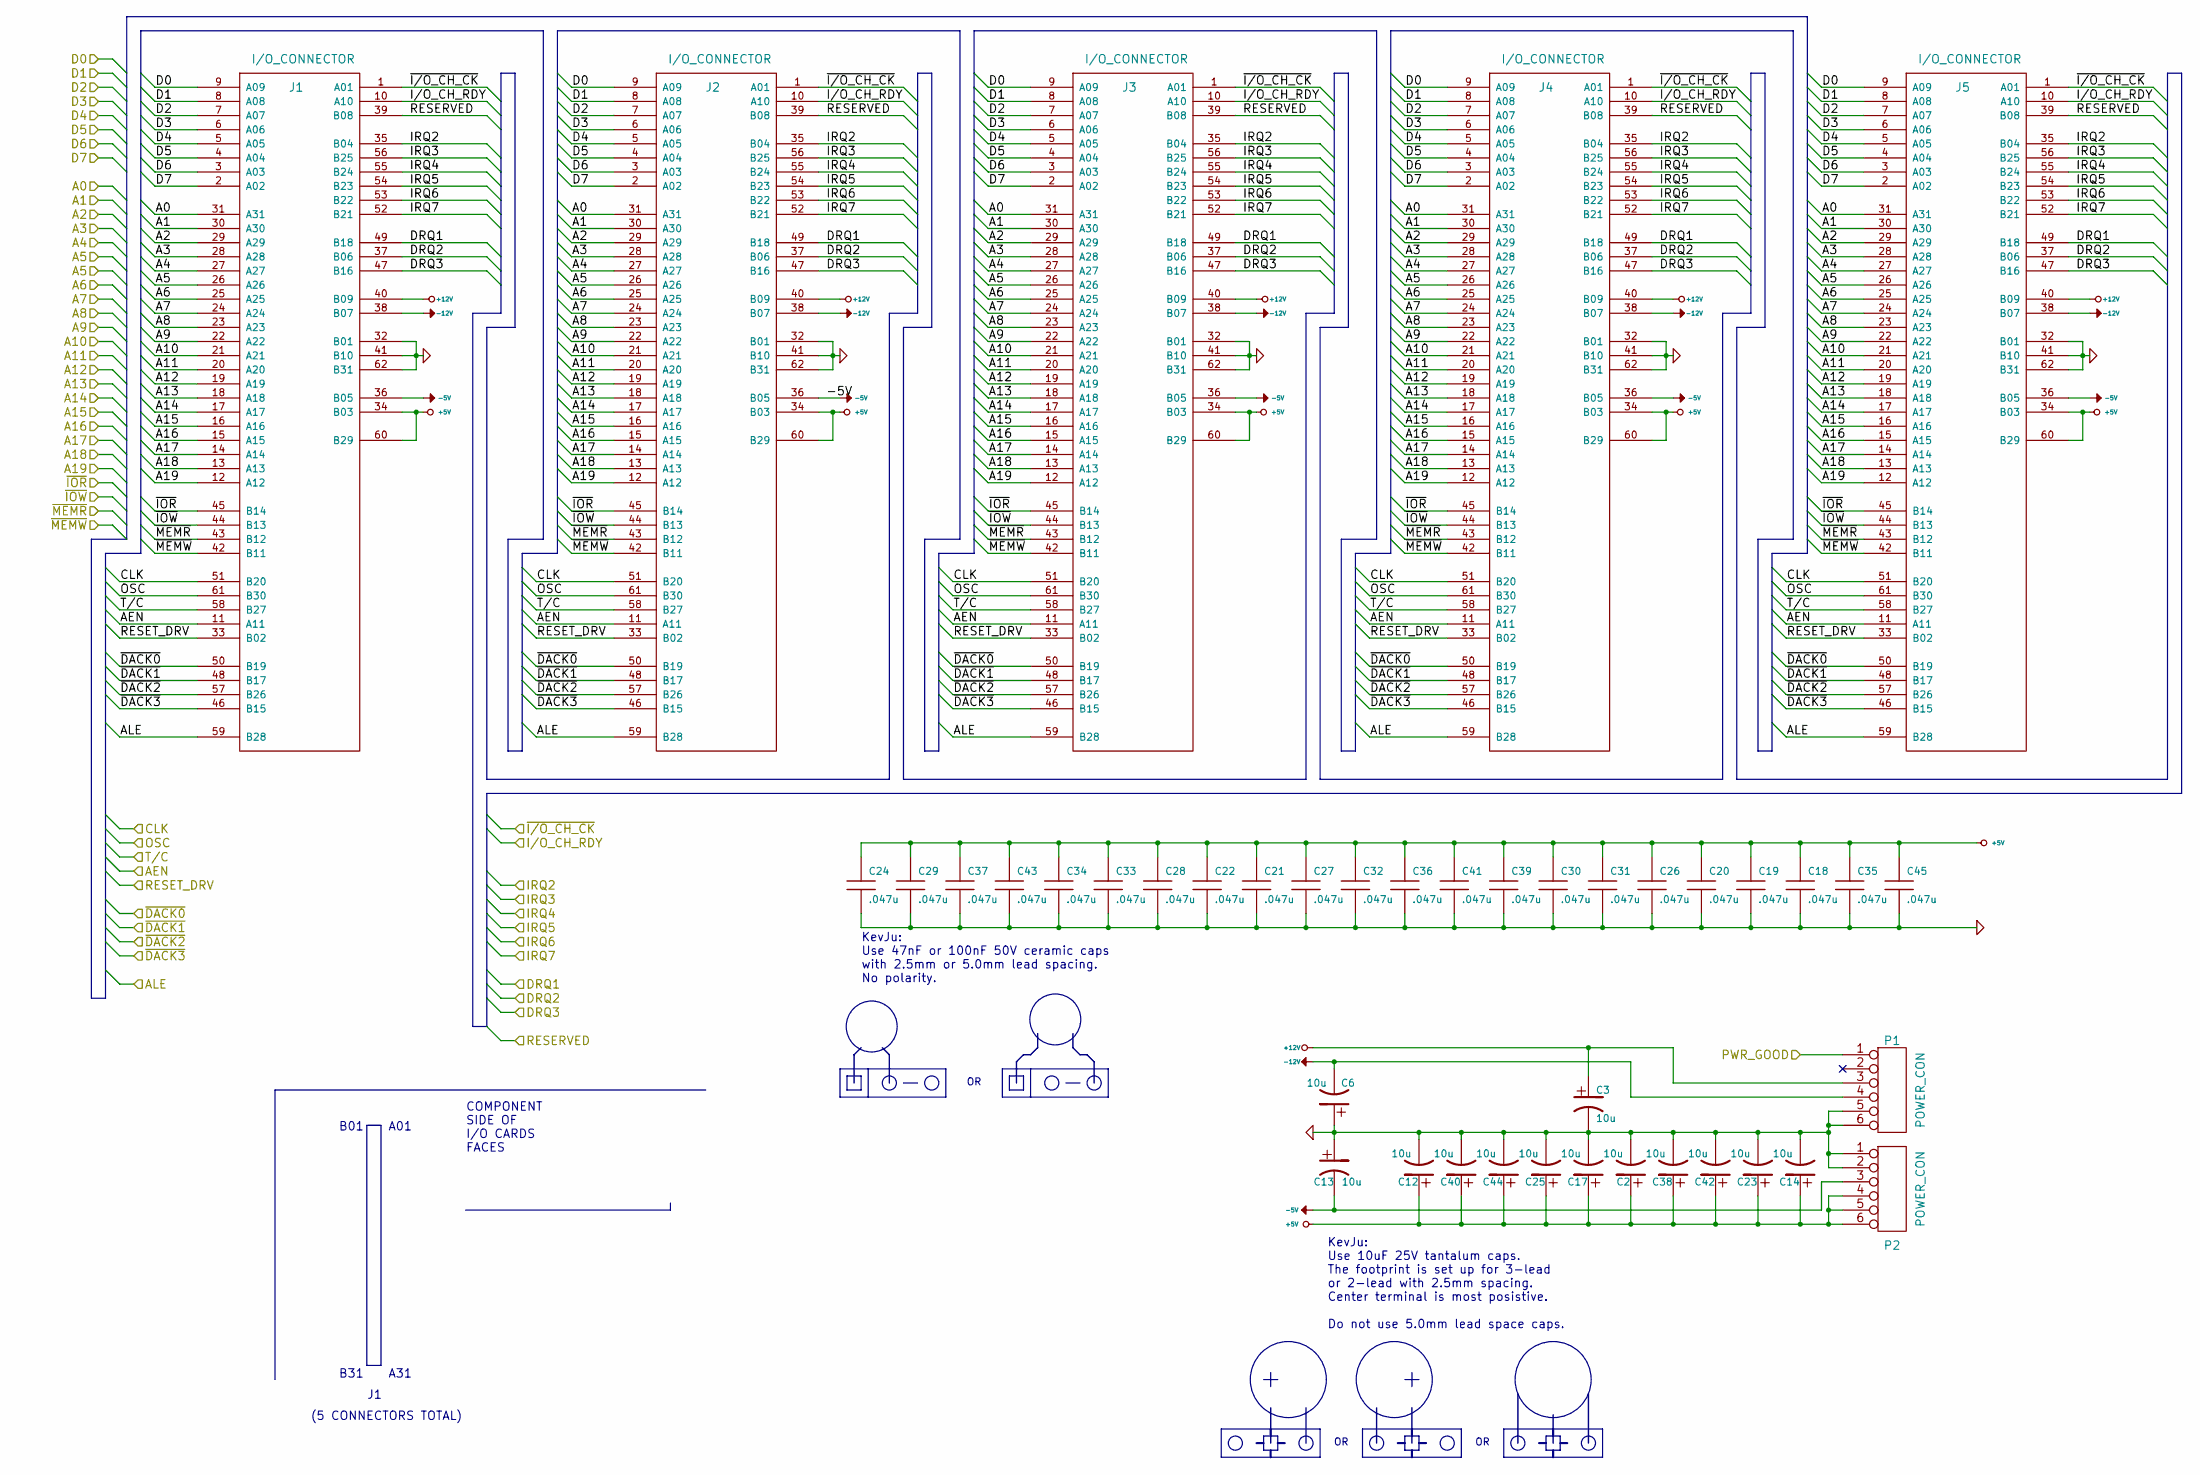
[picture p16: schematic SHEET10.kicad_sch]

Parts:
C2, C3, C6, C12, C13, C14, C17, C23, C25, C38, C40, C42, C44: 10u; C_3PIN
C18, C19, C20, C21, C22, C24, C26, C27, C28, C29, C30, C31, C32, C33, C34, C35, C36, C37, C39, C41, C43, C45: .047u; C_254_508_2PIN
J1, J2, J3, J4, J5: I/O_CONNECTOR; 62PinEdgeIOConnector
P1, P2: POWER_CON

Connections:
+5V: C2.1, C12.1, C14.1, C17.1, C18.1, C19.1, C20.1, C21.1, C22.1, C23.1, C24.1, C25.1, C26.1, C27.1, C28.1, C29.1, C30.1, C31.1, C32.1, C33.1, C34.1, C35.1, C36.1, C37.1, C38.1, C39.1, C40.1, C41.1, C42.1, C43.1, C44.1, C45.1, J1.34 (B03), J1.60 (B29), J2.34 (B03), J2.60 (B29), J3.34 (B03), J3.60 (B29), J4.34 (B03), J4.60 (B29), J5.34 (B03), J5.60 (B29), P2.4, P2.5, P2.6
+12V: C3.1, J1.40 (B09), J2.40 (B09), J3.40 (B09), J4.40 (B09), J5.40 (B09), P1.3
-5V: C13.2, J1.36 (B05), J2.36 (B05), J3.36 (B05), J4.36 (B05), J5.36 (B05), P2.3
-12V: C6.2, J1.38 (B07), J2.38 (B07), J3.38 (B07), J4.38 (B07), J5.38 (B07), P1.4
A0: J1.31 (A31), J2.31 (A31), J3.31 (A31), J4.31 (A31), J5.31 (A31)
A1: J1.30 (A30), J2.30 (A30), J3.30 (A30), J4.30 (A30), J5.30 (A30)
A2: J1.29 (A29), J2.29 (A29), J3.29 (A29), J4.29 (A29), J5.29 (A29)
A3: J1.28 (A28), J2.28 (A28), J3.28 (A28), J4.28 (A28), J5.28 (A28)
A4: J1.27 (A27), J2.27 (A27), J3.27 (A27), J4.27 (A27), J5.27 (A27)
A5: J1.26 (A26), J2.26 (A26), J3.26 (A26), J4.26 (A26), J5.26 (A26)
A6: J1.25 (A25), J2.25 (A25), J3.25 (A25), J4.25 (A25), J5.25 (A25)
A7: J1.24 (A24), J2.24 (A24), J3.24 (A24), J4.24 (A24), J5.24 (A24)
A8: J1.23 (A23), J2.23 (A23), J3.23 (A23), J4.23 (A23), J5.23 (A23)
A9: J1.22 (A22), J2.22 (A22), J3.22 (A22), J4.22 (A22), J5.22 (A22)
A10: J1.21 (A21), J2.21 (A21), J3.21 (A21), J4.21 (A21), J5.21 (A21)
A11: J1.20 (A20), J2.20 (A20), J3.20 (A20), J4.20 (A20), J5.20 (A20)
A12: J1.19 (A19), J2.19 (A19), J3.19 (A19), J4.19 (A19), J5.19 (A19)
A13: J1.18 (A18), J2.18 (A18), J3.18 (A18), J4.18 (A18), J5.18 (A18)
A14: J1.17 (A17), J2.17 (A17), J3.17 (A17), J4.17 (A17), J5.17 (A17)
A15: J1.16 (A16), J2.16 (A16), J3.16 (A16), J4.16 (A16), J5.16 (A16)
A16: J1.15 (A15), J2.15 (A15), J3.15 (A15), J4.15 (A15), J5.15 (A15)
A17: J1.14 (A14), J2.14 (A14), J3.14 (A14), J4.14 (A14), J5.14 (A14)
A18: J1.13 (A13), J2.13 (A13), J3.13 (A13), J4.13 (A13), J5.13 (A13)
A19: J1.12 (A12), J2.12 (A12), J3.12 (A12), J4.12 (A12), J5.12 (A12)
AEN: J1.11 (A11), J2.11 (A11), J3.11 (A11), J4.11 (A11), J5.11 (A11)
ALE: J1.59 (B28), J2.59 (B28), J3.59 (B28), J4.59 (B28), J5.59 (B28)
CLK: J1.51 (B20), J2.51 (B20), J3.51 (B20), J4.51 (B20), J5.51 (B20)
D0: J1.9 (A09), J2.9 (A09), J3.9 (A09), J4.9 (A09), J5.9 (A09)
D1: J1.8 (A08), J2.8 (A08), J3.8 (A08), J4.8 (A08), J5.8 (A08)
D2: J1.7 (A07), J2.7 (A07), J3.7 (A07), J4.7 (A07), J5.7 (A07)
D3: J1.6 (A06), J2.6 (A06), J3.6 (A06), J4.6 (A06), J5.6 (A06)
D4: J1.5 (A05), J2.5 (A05), J3.5 (A05), J4.5 (A05), J5.5 (A05)
D5: J1.4 (A04), J2.4 (A04), J3.4 (A04), J4.4 (A04), J5.4 (A04)
D6: J1.3 (A03), J2.3 (A03), J3.3 (A03), J4.3 (A03), J5.3 (A03)
D7: J1.2 (A02), J2.2 (A02), J3.2 (A02), J4.2 (A02), J5.2 (A02)
DRQ1: J1.49 (B18), J2.49 (B18), J3.49 (B18), J4.49 (B18), J5.49 (B18)
DRQ2: J1.37 (B06), J2.37 (B06), J3.37 (B06), J4.37 (B06), J5.37 (B06)
DRQ3: J1.47 (B16), J2.47 (B16), J3.47 (B16), J4.47 (B16), J5.47 (B16)
GND: C2.2, C3.2, C6.1, C12.2, C13.1, C14.2, C17.2, C18.2, C19.2, C20.2, C21.2, C22.2, C23.2, C24.2, C25.2, C26.2, C27.2, C28.2, C29.2, C30.2, C31.2, C32.2, C33.2, C34.2, C35.2, C36.2, C37.2, C38.2, C39.2, C40.2, C41.2, C42.2, C43.2, C44.2, C45.2, J1.32 (B01), J1.41 (B10), J1.62 (B31), J2.32 (B01), J2.41 (B10), J2.62 (B31), J3.32 (B01), J3.41 (B10), J3.62 (B31), J4.32 (B01), J4.41 (B10), J4.62 (B31), J5.32 (B01), J5.41 (B10), J5.62 (B31), P1.5, P1.6, P2.1, P2.2
I/O_CH_RDY: J1.10 (A10), J2.10 (A10), J3.10 (A10), J4.10 (A10), J5.10 (A10)
IRQ2: J1.35 (B04), J2.35 (B04), J3.35 (B04), J4.35 (B04), J5.35 (B04)
IRQ3: J1.56 (B25), J2.56 (B25), J3.56 (B25), J4.56 (B25), J5.56 (B25)
IRQ4: J1.55 (B24), J2.55 (B24), J3.55 (B24), J4.55 (B24), J5.55 (B24)
IRQ5: J1.54 (B23), J2.54 (B23), J3.54 (B23), J4.54 (B23), J5.54 (B23)
IRQ6: J1.53 (B22), J2.53 (B22), J3.53 (B22), J4.53 (B22), J5.53 (B22)
IRQ7: J1.52 (B21), J2.52 (B21), J3.52 (B21), J4.52 (B21), J5.52 (B21)
OSC: J1.61 (B30), J2.61 (B30), J3.61 (B30), J4.61 (B30), J5.61 (B30)
PWR_GOOD: P1.1
RESERVED: J1.39 (B08), J2.39 (B08), J3.39 (B08), J4.39 (B08), J5.39 (B08)
RESET_DRV: J1.33 (B02), J2.33 (B02), J3.33 (B02), J4.33 (B02), J5.33 (B02)
T/C: J1.58 (B27), J2.58 (B27), J3.58 (B27), J4.58 (B27), J5.58 (B27)
~DACK0: J1.50 (B19), J2.50 (B19), J3.50 (B19), J4.50 (B19), J5.50 (B19)
~DACK1: J1.48 (B17), J2.48 (B17), J3.48 (B17), J4.48 (B17), J5.48 (B17)
~DACK2: J1.57 (B26), J2.57 (B26), J3.57 (B26), J4.57 (B26), J5.57 (B26)
~DACK3: J1.46 (B15), J2.46 (B15), J3.46 (B15), J4.46 (B15), J5.46 (B15)
~I/O_CH_CK: J1.1 (A01), J2.1 (A01), J3.1 (A01), J4.1 (A01), J5.1 (A01)
~IOR: J1.45 (B14), J2.45 (B14), J3.45 (B14), J4.45 (B14), J5.45 (B14)
~IOW: J1.44 (B13), J2.44 (B13), J3.44 (B13), J4.44 (B13), J5.44 (B13)
~MEMR: J1.43 (B12), J2.43 (B12), J3.43 (B12), J4.43 (B12), J5.43 (B12)
~MEMW: J1.42 (B11), J2.42 (B11), J3.42 (B11), J4.42 (B11), J5.42 (B11)

Notes on the sheet:
B31
KevJu: Use 47nF or 100nF 50V ceramic caps with 2.5mm or 5.0mm lead spacing. No polarity.
KevJu: Use 10uF 25V tantalum caps. The footprint is set up for 3-lead or 2-lead with 2.5mm spacing. Center terminal is most posistive. Do not use 5.0mm lead space caps.
(5 CONNECTORS TOTAL)
COMPONENT SIDE OF I/O CARDS FACES
B01
A01
A31
