kev-ju/PC-Retro-MTM/SHET4.kicad_sch

## KiCad design SHET4.kicad_sch (2026-03-31)

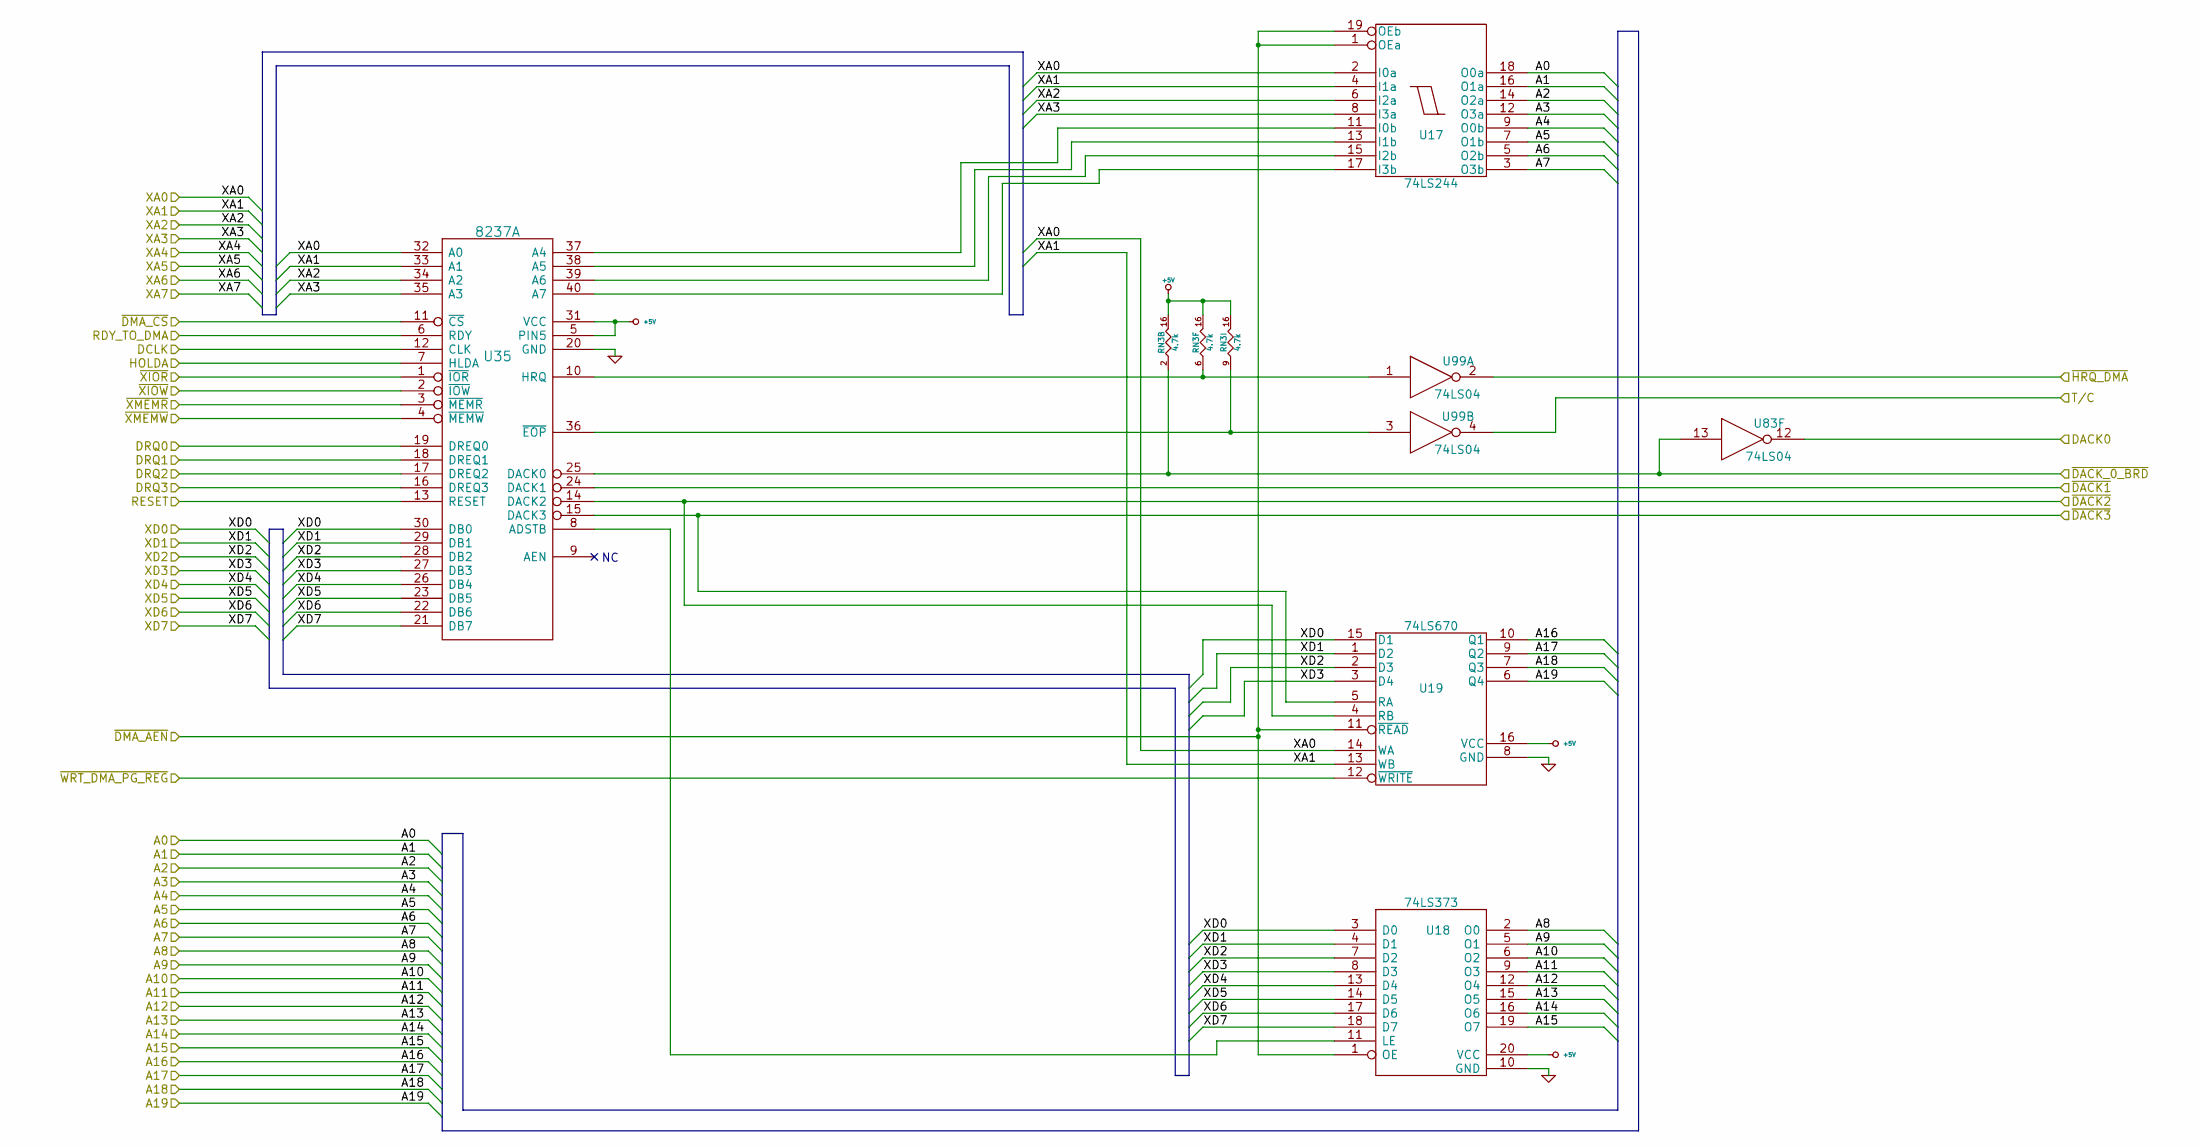
[picture p17: schematic SHET4.kicad_sch]

Parts:
RN3: 4.7k; DIP-16__300
U17: 74LS244; DIP-20__300
U18: 74LS373; DIP-20__300
U19: 74LS670; DIP-16__300
U35: 8237A; DIP-40__600
U83, U99: 74LS04; DIP-14__300

Connections:
+5V: RN3.16, U18.20 (VCC), U19.16 (VCC), U35.5 (PIN5), U35.31 (VCC)
A0: U17.18 (O0a)
A1: U17.16 (O1a)
A2: U17.14 (O2a)
A3: U17.12 (O3a)
A4: U17.9 (O0b)
A5: U17.7 (O1b)
A6: U17.5 (O2b)
A7: U17.3 (O3b)
A8: U18.2 (O0)
A9: U18.5 (O1)
A10: U18.6 (O2)
A11: U18.9 (O3)
A12: U18.12 (O4)
A13: U18.15 (O5)
A14: U18.16 (O6)
A15: U18.19 (O7)
A16: U19.10 (Q1)
A17: U19.9 (Q2)
A18: U19.7 (Q3)
A19: U19.6 (Q4)
DACK0: U83.12
DCLK: U35.12 (CLK)
DRQ0: U35.19 (DREQ0)
DRQ1: U35.18 (DREQ1)
DRQ2: U35.17 (DREQ2)
DRQ3: U35.16 (DREQ3)
GND: U18.10 (GND), U19.8 (GND), U35.20 (GND)
HOLDA: U35.7 (HLDA)
unnamed: RN3.6 (P15), U35.10 (HRQ), U99.1
unnamed: RN3.9 (P15), U35.36 (~EOP), U99.3
unnamed: U17.11 (I0b), U35.37 (A4)
unnamed: U17.13 (I1b), U35.38 (A5)
unnamed: U17.15 (I2b), U35.39 (A6)
unnamed: U17.17 (I3b), U35.40 (A7)
unnamed: U18.11 (LE), U35.8 (ADSTB)
RDY_TO_DMA: U35.6 (RDY)
RESET: U35.13 (RESET)
T/C: U99.4
XA0: U17.2 (I0a), U19.14 (WA), U35.32 (A0)
XA1: U17.4 (I1a), U19.13 (WB), U35.33 (A1)
XA2: U17.6 (I2a), U35.34 (A2)
XA3: U17.8 (I3a), U35.35 (A3)
XD0: U18.3 (D0), U19.15 (D1), U35.30 (DB0)
XD1: U18.4 (D1), U19.1 (D2), U35.29 (DB1)
XD2: U18.7 (D2), U19.2 (D3), U35.28 (DB2)
XD3: U18.8 (D3), U19.3 (D4), U35.27 (DB3)
XD4: U18.13 (D4), U35.26 (DB4)
XD5: U18.14 (D5), U35.23 (DB5)
XD6: U18.17 (D6), U35.22 (DB6)
XD7: U18.18 (D7), U35.21 (DB7)
~DACK1: U35.24 (DACK1)
~DACK2: U19.4 (RB), U35.14 (DACK2)
~DACK3: U19.5 (RA), U35.15 (DACK3)
~DACK_0_BRD: RN3.2 (P15), U35.25 (DACK0), U83.13
~DMA_AEN: U17.1 (OEa), U17.19 (OEb), U18.1 (OE), U19.11 (~READ)
~DMA_CS: U35.11 (~CS)
~HRQ_DMA: U99.2
~WRT_DMA_PG_REG: U19.12 (~WRITE)
~XIOR: U35.1 (~IOR)
~XIOW: U35.2 (~IOW)
~XMEMR: U35.3 (~MEMR)
~XMEMW: U35.4 (~MEMW)
